KaylaR2040/SD_OrionBMS/src/bq79616.c

/* ===========================================================================
 * File: bq79616.c
 * Description: Driver for TI BQ79616 battery monitor IC.
 *
 * Notes:
 *   - This driver is designed for a single stacked device; multi-device support
 *     is possible but untested.
 *   - All functions are thread-compatible but not thread-safe; caller must
 *     serialize access to the bus and device.
 * ===========================================================================
 */

#include "master.h"


/* Key register addresses (word addresses from datasheet) */

/* Table 9-10 REQ_TYPE encoding (bits 6:4) */
typedef enum
{
    BQ_REQ_SINGLE_READ          = 0u, /* 000 */
    BQ_REQ_SINGLE_WRITE         = 1u, /* 001 */
    BQ_REQ_STACK_READ           = 2u, /* 010 */
    BQ_REQ_STACK_WRITE          = 3u, /* 011 */
    BQ_REQ_BROADCAST_READ       = 4u, /* 100 */
    BQ_REQ_BROADCAST_WRITE      = 5u, /* 101 */
    BQ_REQ_BROADCAST_WRITE_REV  = 6u  /* 110 */
    /* 111 reserved */
} bq_req_type_t;

static uint8_t tx_buf[BQ_TX_MAX];
static uint8_t rx_buf[BQ_RX_MAX];

// Function Declarations
void bq_pin_tx_to_gpio(void);
void bq_pin_tx_to_uart(void);
void bq_pin_tx_set(GPIO_PinState state);
void bq_delay_us(uint32_t us);
void bq_drive_wake_pulse(uint32_t pulse_us);
void bq_enable_dwt(void);
void bq_log_hex_internal(const char *label, const uint8_t *buf, size_t len);
static int bq79616_read_all_cells_with_timeout_(uint16_t *out_mv, size_t cell_count, uint32_t timeout_ms);

/* ------------------------------ CRC16-IBM --------------------------------- */
/* Reflected polynomial 0xA001, init 0xFFFF */
static const uint16_t crc16_table[256] = {
    0x0000,0xC0C1,0xC181,0x0140,0xC301,0x03C0,0x0280,0xC241,0xC601,0x06C0,0x0780,0xC741,0x0500,0xC5C1,0xC481,0x0440,
    0xCC01,0x0CC0,0x0D80,0xCD41,0x0F00,0xCFC1,0xCE81,0x0E40,0x0A00,0xCAC1,0xCB81,0x0B40,0xC901,0x09C0,0x0880,0xC841,
    0xD801,0x18C0,0x1980,0xD941,0x1B00,0xDBC1,0xDA81,0x1A40,0x1E00,0xDEC1,0xDF81,0x1F40,0xDD01,0x1DC0,0x1C80,0xDC41,
    0x1400,0xD4C1,0xD581,0x1540,0xD701,0x17C0,0x1680,0xD641,0xD201,0x12C0,0x1380,0xD341,0x1100,0xD1C1,0xD081,0x1040,
    0xF001,0x30C0,0x3180,0xF141,0x3300,0xF3C1,0xF281,0x3240,0x3600,0xF6C1,0xF781,0x3740,0xF501,0x35C0,0x3480,0xF441,
    0x3C00,0xFCC1,0xFD81,0x3D40,0xFF01,0x3FC0,0x3E80,0xFE41,0xFA01,0x3AC0,0x3B80,0xFB41,0x3900,0xF9C1,0xF881,0x3840,
    0x2800,0xE8C1,0xE981,0x2940,0xEB01,0x2BC0,0x2A80,0xEA41,0xEE01,0x2EC0,0x2F80,0xEF41,0x2D00,0xEDC1,0xEC81,0x2C40,
    0xE401,0x24C0,0x2580,0xE541,0x2700,0xE7C1,0xE681,0x2640,0x2200,0xE2C1,0xE381,0x2340,0xE101,0x21C0,0x2080,0xE041,
    0xA001,0x60C0,0x6180,0xA141,0x6300,0xA3C1,0xA281,0x6240,0x6600,0xA6C1,0xA781,0x6740,0xA501,0x65C0,0x6480,0xA441,
    0x6C00,0xACC1,0xAD81,0x6D40,0xAF01,0x6FC0,0x6E80,0xAE41,0xAA01,0x6AC0,0x6B80,0xAB41,0x6900,0xA9C1,0xA881,0x6840,
    0x7800,0xB8C1,0xB981,0x7940,0xBB01,0x7BC0,0x7A80,0xBA41,0xBE01,0x7EC0,0x7F80,0xBF41,0x7D00,0xBDC1,0xBC81,0x7C40,
    0xB401,0x74C0,0x7580,0xB541,0x7700,0xB7C1,0xB681,0x7640,0x7200,0xB2C1,0xB381,0x7340,0xB101,0x71C0,0x7080,0xB041,
    0x5000,0x90C1,0x9181,0x5140,0x9301,0x53C0,0x5280,0x9241,0x9601,0x56C0,0x5780,0x9741,0x5500,0x95C1,0x9481,0x5440,
    0x9C01,0x5CC0,0x5D80,0x9D41,0x5F00,0x9FC1,0x9E81,0x5E40,0x5A00,0x9AC1,0x9B81,0x5B40,0x9901,0x59C0,0x5880,0x9841,
    0x8801,0x48C0,0x4980,0x8941,0x4B00,0x8BC1,0x8A81,0x4A40,0x4E00,0x8EC1,0x8F81,0x4F40,0x8D01,0x4DC0,0x4C80,0x8C41,
    0x4400,0x84C1,0x8581,0x4540,0x8701,0x47C0,0x4680,0x8641,0x8201,0x42C0,0x4380,0x8341,0x4100,0x81C1,0x8081,0x4040
};

uint16_t bq79616_crc16(const uint8_t *data, uint16_t len)
{
    uint16_t crc = BQ_CRC16_INIT_VALUE;
    for (uint16_t i = 0; i < len; i++) {
        uint8_t idx = (uint8_t)(crc ^ data[i]);
        crc = (uint16_t)((crc >> 8) ^ crc16_table[idx]);
    }
    return crc;
}

/* Validate per datasheet: CRC computed across entire frame including CRC must be 0 */
int bq_crc_validate_full_frame(const uint8_t *frame, uint16_t frame_len)
{
    if (!frame || frame_len < BQ_FRAME_CRC_MIN_BYTES) {
        return -1;
    }
    if (bq79616_crc16(frame, frame_len) == 0u) {
        return 0;
    }
    return -2;
}








/* ----------------------------- INIT byte helpers -------------------------- */
/*
 * Command INIT (Table 9-10):
 *   bit7 = 1
 *   bits6:4 = REQ_TYPE
 *   bit3 = RSVD (0)
 *   bits2:0 = DATA_SIZE (000->1 byte ... 111->8 bytes)
 *
 * data_bytes:
 *   - writes: number of write bytes (1..8)
 *   - reads:  must be 1 because DATA[0] carries (bytes_to_return - 1)
 */
uint8_t bq_init_cmd(bq_req_type_t req, uint8_t data_bytes)
{
    if (data_bytes < BQ_CMD_DATA_BYTES_MIN) data_bytes = BQ_CMD_DATA_BYTES_MIN;
    if (data_bytes > BQ_CMD_DATA_BYTES_MAX) data_bytes = BQ_CMD_DATA_BYTES_MAX;

    uint8_t data_size_bits = (uint8_t)((data_bytes - 1u) & BQ_CMD_REQ_TYPE_MASK);
    return (uint8_t)((BQ_CMD_FRAME_TYPE << 7) | (((uint8_t)req & BQ_CMD_REQ_TYPE_MASK) << 4) | data_size_bits);
}

/*
 * Response INIT (Table 9-10 response side):
 *   bit7 = 0
 *   bits6:0 = RESPONSE_BYTE (0x00->1 byte ... 0x7F->128 bytes)
 */
uint8_t bq_rsp_len_from_init(uint8_t init_byte, uint8_t *out_len)
{
    if (!out_len) return 1u;
    if ((init_byte & BQ_INIT_RESPONSE_FLAG_MASK) != 0u) return 2u; /* not a response frame */
    uint8_t n = (uint8_t)(init_byte & BQ_INIT_RESPONSE_LEN_MASK);
    *out_len = (uint8_t)(n + 1u);
    return 0u;
}

/* ---------------------------- UART helpers (HAL) -------------------------- */

int bq_uart_tx(const uint8_t *buf, uint16_t len, uint32_t timeout_ms)
{
    if (!buf || len == 0u) return -1;
    if (HAL_UART_Transmit(&uart_bq79616, (uint8_t *)buf, len, timeout_ms) == HAL_OK) {
        return 0;
    }
    return -2;
}

int bq_uart_rx(uint8_t *buf, uint16_t len, uint32_t timeout_ms)
{
    if (!buf || len == 0u) return -1;
    if (HAL_UART_Receive(&uart_bq79616, buf, len, timeout_ms) == HAL_OK) {
        return 0;
    }
    return -2;
}

int bq_uart_txrx(const uint8_t *tx, uint16_t tx_len, uint8_t *rx, uint16_t rx_len, uint32_t timeout_ms)
{
    if (!tx || !rx || tx_len == 0u || rx_len == 0u) {
        return -1;
    }

    /* Sequential TX then RX (half-duplex safe) */
    if (HAL_UART_Transmit(&uart_bq79616, (uint8_t *)tx, tx_len, timeout_ms) != HAL_OK) {
        return -2;
    }
    if (HAL_UART_Receive(&uart_bq79616, rx, rx_len, timeout_ms) != HAL_OK) {
        return -3;
    }
    return 0;
}

/* Public single-device wrappers */
int bq79616_write(uint8_t dev_id, uint16_t reg_addr, const uint8_t *data, uint8_t len)
{
    return bq7961x_single_write(dev_id, reg_addr, data, len, BQ_FAST_TIMEOUT_MS);
}


/* Optional: explicitly set baudrate on the configured handle */
int bq7961x_uart_set_baud(uint32_t baudrate)
{
    uart_bq79616.Init.BaudRate = baudrate;
    if (HAL_UART_DeInit(&uart_bq79616) != HAL_OK) return -1;
    if (HAL_UART_Init(&uart_bq79616) != HAL_OK) return -2;
    return 0;
}

void bq_pin_tx_to_gpio(void)
{
    HAL_GPIO_DeInit(GPIOC, GPIO_PIN_4);
    GPIO_InitTypeDef g = {0};
    g.Pin = GPIO_PIN_4;
    g.Mode = GPIO_MODE_OUTPUT_PP;
    g.Pull = GPIO_PULLUP;
    g.Speed = GPIO_SPEED_FREQ_HIGH;
    HAL_GPIO_Init(GPIOC, &g);
}

void bq_pin_tx_set(GPIO_PinState state)
{
    HAL_GPIO_WritePin(BQ_GPIO_PORT, BQ_GPIO_PIN, state);
}

void bq_pin_tx_to_uart(void)
{
    HAL_GPIO_DeInit(GPIOC, GPIO_PIN_4);
    GPIO_InitTypeDef g = {0};
    g.Pin = GPIO_PIN_4;
    g.Mode = GPIO_MODE_AF_PP;
    g.Pull = GPIO_PULLUP;
    g.Speed = GPIO_SPEED_FREQ_VERY_HIGH;
    g.Alternate = GPIO_AF7_USART1;
    HAL_GPIO_Init(GPIOC, &g);
}

int bq_uart_reinit(void)
{
    bq_pin_tx_to_uart();
    if (HAL_UART_Init(&uart_bq79616) == HAL_OK) {
        return 0;
    }
    return -1;
}




void bq_drive_wake_pulse(uint32_t pulse_us)
{
    /* Host manually drives TX low to generate UART wake ping per TI spec */
    bq_pin_tx_set(GPIO_LOW);
    bq_delay_us(pulse_us);
    bq_pin_tx_set(GPIO_HIGH);
}


void bq_enable_dwt(void)
{
    /* Enable DWT cycle counter for sub-ms delays if not already on */
    if (!(CoreDebug->DEMCR & CoreDebug_DEMCR_TRCENA_Msk)) {
        CoreDebug->DEMCR |= CoreDebug_DEMCR_TRCENA_Msk;
    }
    if (!(DWT->CTRL & DWT_CTRL_CYCCNTENA_Msk)) {
        DWT->CYCCNT = 0;
        DWT->CTRL |= DWT_CTRL_CYCCNTENA_Msk;
    }
}

void bq_delay_us(uint32_t us)
{
    bq_enable_dwt();
    uint32_t cycles = (SystemCoreClock / 1000000u) * us;
    uint32_t start = DWT->CYCCNT;
    while ((DWT->CYCCNT - start) < cycles) {
        __NOP();
    }
}

/* TI-style delay wrappers */
void delayus(uint16_t us)
{
    bq_delay_us(us);
}

void delayms(uint16_t ms)
{
    HAL_Delay(ms);
}

void bq_log_hex(const char *label, const uint8_t *buf, size_t len)
{
    const char *tag = (label) ? label : "BUF";
    if (!buf || len == 0u) {
        LOG_PRINT(LOG_TYPE_INFO, "%s: <empty>", tag);
        return;
    }

    char line[BQ_HEX_LOG_LINE_MAX_CHARS];
    size_t pos = 0u;
    pos += (size_t)snprintf(line + pos, sizeof(line) - pos, "%s (%uB): ", tag, (unsigned)len);

    for (size_t i = 0; i < len; i++) {
        if ((pos + BQ_HEX_LOG_ELLIPSIS_RESERVE) >= sizeof(line)) {
            pos += (size_t)snprintf(line + pos, sizeof(line) - pos, "...");
            break;
        }
        pos += (size_t)snprintf(line + pos, sizeof(line) - pos, "%02X ", buf[i]);
    }

    LOG_PRINT(LOG_TYPE_INFO, "%s", line);
}

/* ---------------------- Frame builder (command frames) -------------------- */

int bq79616_build_single_read_frame(uint16_t reg_addr, uint8_t n_minus_1, uint8_t *out, size_t out_max, size_t *out_len)
{
    if (!out || !out_len) {
        return -1;
    }
    if (out_max < BQ_SINGLE_READ_FRAME_LEN) {
        return -2;
    }

    out[0] = BQ_SINGLE_READ_INIT_VALUE; /* INIT: Single Device Read, DATA_SIZE=1 byte */
    out[1] = (uint8_t)(DEVICE_ADDR & BQ_DEV_ADDR_MAX);
    out[2] = (uint8_t)((reg_addr >> 8) & BQ_BYTE_MASK);
    out[3] = (uint8_t)(reg_addr & BQ_BYTE_MASK);
    out[4] = n_minus_1; /* number of bytes to read minus one */

    /* CRC-16-IBM across bytes [0..4], appended as [CRC_H][CRC_L] */
    uint16_t crc = bq79616_crc16(out, 5u);
    out[5] = (uint8_t)((crc >> 8) & BQ_BYTE_MASK);
    out[6] = (uint8_t)(crc & BQ_BYTE_MASK);

    *out_len = BQ_SINGLE_READ_FRAME_LEN;
    return 0;
}

int bq79616_read_partid_once(uint8_t *partid_out)
{
    LOG_PRINT(LOG_TYPE_INFO, CYAN, "=== BQ79616 bring-up: PARTID read ===");

    uint8_t val = 0u;
    int bq_status = bq7961x_single_read(DEVICE_ADDR, BQ_PARTID_REG, &val, 1u, BQ_FIRST_READ_TIMEOUT_MS);
    if (bq_status != 0) {
        LOG_PRINT(LOG_TYPE_ERROR, CYAN, "PARTID: read failed (bq_status=%d)", bq_status);
        return bq_status;
    }

    if (partid_out) {
        *partid_out = val;
    }

    LOG_PRINT(LOG_TYPE_INFO, CYAN, "PARTID: expected=0x%02X received=0x%02X", BQ_PARTID_EXPECTED, val);
    return (val == BQ_PARTID_EXPECTED) ? 0 : 1;
}

int bq_build_cmd_frame(uint8_t *out, uint16_t out_max, bq_req_type_t req, uint8_t dev_addr, uint16_t reg_addr, const uint8_t *data, uint16_t data_len, uint16_t *out_len)
{
    if (!out || !out_len) return -1;
    *out_len = 0u;

    bool include_dev = (req == BQ_REQ_SINGLE_READ || req == BQ_REQ_SINGLE_WRITE);

    if (include_dev) {
        if (dev_addr > BQ_DEV_ADDR_MAX) return -2;
    }

    if (data_len < BQ_CMD_DATA_BYTES_MIN) return -3;

    /* Command DATA_SIZE is 3 bits => max 8 data bytes in a command frame */
    if (data_len > BQ_WRITE_MAX_BYTES) return -4;

    uint16_t include_dev_len = 0u;
    if (include_dev) {
        include_dev_len = 1u;
    }

    uint16_t needed = (uint16_t)(1u + include_dev_len + 2u + data_len + 2u);
    if (needed > out_max) return -5;

    uint16_t idx = 0u;

    out[idx++] = bq_init_cmd(req, (uint8_t)data_len);

    if (include_dev) {
        /* Table 9-11: bits7:6 should be 0, bits5:0 is device address */
        out[idx++] = (uint8_t)(dev_addr & BQ_DEV_ADDR_MAX);
    }

    /* Table 9-12: REG_ADR is 2 bytes (MSB then LSB) */
    out[idx++] = (uint8_t)((reg_addr >> 8) & BQ_BYTE_MASK);
    out[idx++] = (uint8_t)(reg_addr & BQ_BYTE_MASK);

    /* Table 9-13: DATA bytes */
    if (data && data_len) {
        memcpy(&out[idx], data, data_len);
    } else {
        memset(&out[idx], BQ_AUTO_ADDR_DUMMY_WRITE_VALUE, data_len);
    }
    idx = (uint16_t)(idx + data_len);

    /*
     * CRC bytes (datasheet):
     *   CRC remainder is appended so receiver CRC over entire frame (incl CRC) becomes 0.
     * We append CRC LSB then CRC MSB (matches TI ref style / common IBM CRC framing).
     */
    uint16_t crc = bq79616_crc16(out, idx);
    out[idx++] = (uint8_t)(crc & BQ_BYTE_MASK);         /* CRC_L */
    out[idx++] = (uint8_t)((crc >> 8) & BQ_BYTE_MASK);  /* CRC_H */

    *out_len = idx;
    return 0;
}

/* ---------------------- Internal send command APIs ------------------------ */
int bq7961x_single_write(uint8_t dev_addr, uint16_t reg_addr, const uint8_t *data, uint8_t len, uint32_t timeout_ms)
{
    if (len < BQ_CMD_DATA_BYTES_MIN || len > BQ_CMD_DATA_BYTES_MAX) return -1;

    uint16_t frame_len = 0u;
    int bq_status = bq_build_cmd_frame(tx_buf, sizeof(tx_buf),
                                BQ_REQ_SINGLE_WRITE,
                                dev_addr,
                                reg_addr,
                                data,
                                len,
                                &frame_len);
    if (bq_status != 0) return bq_status;

    return bq_uart_tx(tx_buf, frame_len, timeout_ms);
}

int bq7961x_single_read(uint8_t dev_addr, uint16_t reg_addr, uint8_t *out, uint8_t out_len, uint32_t timeout_ms)
{
    if (!out) return -1;
    if (out_len < 1u || out_len > BQ_READ_MAX_BYTES) return -2;

    /*
     * Per Table 9-13 (READ):
     *   DATA[0] specifies (bytes_to_return - 1)
     * So read request always has exactly 1 data byte.
     */
    uint8_t req_data = (uint8_t)(out_len - 1u);

    uint16_t cmd_len = 0u; // To be set by bq_build_cmd_frame
    int bq_status = bq_build_cmd_frame(tx_buf, sizeof(tx_buf),
                                BQ_REQ_SINGLE_READ,
                                dev_addr,
                                reg_addr,
                                &req_data,
                                1u,
                                &cmd_len);
    if (bq_status != 0) return bq_status;

    /* TX read request */
    bq_status = bq_uart_tx(tx_buf, cmd_len, timeout_ms);
    if (bq_status != 0) return bq_status;

    /*
     * RX response:
     *   First byte is INIT (bit7 must be 0). It contains (response_bytes-1) in bits6:0.
     */
    uint8_t init = 0u;
    bq_status = bq_uart_rx(&init, sizeof(init), timeout_ms);
    if (bq_status != 0) return -10;

    uint8_t rsp_data_len = 0u;
    if (bq_rsp_len_from_init(init, &rsp_data_len) != 0u) {
        return -11;
    }

    /* Ensure response length matches what you requested */
    if (rsp_data_len != out_len) {
        return -12;
    }

    /*
     * Remaining bytes after INIT:
     *   DEV(1) + REG(2) + DATA(out_len) + Cbq_status(2)
     */
    uint16_t remain = (uint16_t)(1u + 2u + rsp_data_len + 2u);
    if ((1u + remain) > sizeof(rx_buf)) return -13;

    rx_buf[0] = init;
    bq_status = bq_uart_rx(&rx_buf[1], remain, timeout_ms);
    if (bq_status != 0) return -14;

    uint16_t full_len = (uint16_t)(1u + remain);

    /* Cbq_status check across entire response (including Cbq_status) must be 0 */
    bq_status = bq_crc_validate_full_frame(rx_buf, full_len);
    if (bq_status != 0) return -15;

    /* Basic field checks */
    uint8_t rsp_dev = (uint8_t)(rx_buf[1] & BQ_DEV_ADDR_MAX);
    uint16_t rsp_reg = (uint16_t)((rx_buf[2] << 8) | rx_buf[3]);

    if (rsp_dev != (dev_addr & BQ_DEV_ADDR_MAX)) return -16;
    if (rsp_reg != reg_addr) return -17;

    /* Copy payload */
    memcpy(out, &rx_buf[4], rsp_data_len);
    return 0;
}






int bq7961x_broadcast_write(uint16_t reg_addr, const uint8_t *data, uint8_t len, uint32_t timeout_ms)
{
    if (len < BQ_CMD_DATA_BYTES_MIN || len > BQ_CMD_DATA_BYTES_MAX) return -1;

    uint16_t frame_len = 0u;
    int bq_status = bq_build_cmd_frame(tx_buf, sizeof(tx_buf),
                                BQ_REQ_BROADCAST_WRITE,
                                0u,
                                reg_addr,
                                data,
                                len,
                                &frame_len);
    if (bq_status != 0) return bq_status;

    return bq_uart_tx(tx_buf, frame_len, timeout_ms);
}

/* TI-style wake helper */
void bq79616_wake(void)
{
    /* Two 2.5 ms low pulses with UART temporarily released */
    HAL_UART_DeInit(&uart_bq79616);
    bq_pin_tx_to_gpio();

    bq_pin_tx_set(GPIO_LOW);
    delayus(BQ_WAKE_PULSE_US);
    bq_pin_tx_set(GPIO_HIGH);
    bq_pin_tx_to_uart();
    HAL_UART_Init(&uart_bq79616);

    HAL_UART_DeInit(&uart_bq79616);
    bq_pin_tx_to_gpio();

    bq_pin_tx_set(GPIO_LOW);
    delayus(BQ_WAKE_PULSE_US);
    bq_pin_tx_set(GPIO_HIGH);
    bq_pin_tx_to_uart();
    HAL_UART_Init(&uart_bq79616);
}

void bq79616_shutdown(void)
{
    LOG_PRINT(LOG_TYPE_INFO, CYAN, "=== FORCE BQ79616 SHUTDOWN ===");

    /*
     * Stop UART so the TX pin can be manually driven.
     * STM32 TX drives BQ RX.
     */
    HAL_UART_DeInit(&uart_bq79616);
    bq_pin_tx_to_gpio();

    /*
     * Ensure idle-high before the ping starts.
     * A ping is high-low-high, and UART idle is high.
     */
    bq_pin_tx_set(GPIO_HIGH);
    delayus(BQ_SHUTDOWN_IDLE_HIGH_US);

    /*
     * SHUTDOWN ping:
     * Hold BQ RX low for 7 ms to 10 ms.
     * Use 9 ms nominal.
     */
    bq_pin_tx_set(GPIO_LOW);
    delayus(BQ_SHUTDOWN_PING_LOW_US);
    bq_pin_tx_set(GPIO_HIGH);

    /*
     * Wait for the BQ to complete ACTIVE -> SHUTDOWN transition.
     * Datasheet says 20 ms. Use 25 ms margin.
     */
    delayms(BQ_SHUTDOWN_ENTRY_MS);

    /*
     * Leave transport disabled after shutdown, but keep the line high.
     * Do not leave BQ RX low, because that could look like another ping
     * or hold the interface in a bad state.
     */
    bq_pin_tx_set(GPIO_HIGH);

    LOG_PRINT(LOG_TYPE_INFO, CYAN, "=== BQ79616 SHUTDOWN COMPLETE ===");

    Volt_ForceDisable();
}

/* Read cell voltage from ADC (keeps device ACTIVE via periodic communication) */
int bq79616_read_cell_voltage(uint8_t dev_addr, uint8_t cell_channel, uint16_t *voltage_mv)
{
    int bq_status;
    uint8_t data[BQ_SINGLE_CELL_READ_BYTES] = {0};

    if (!voltage_mv) return -1;

    /* Cell voltage registers (2 bytes each):
       VC1=0x0014, VC2=0x0016, VC3=0x0018, VC4=0x001A, etc.
       Each channel offset by 2 bytes */
    uint16_t reg_addr = BQ_CELL_REG_BASE + (cell_channel * BQ_CELL_REG_STRIDE_BYTES);

    /* Read 2 bytes from the voltage register */
    bq_status = bq7961x_single_read(dev_addr, reg_addr, data, sizeof(data), BQ_FAST_TIMEOUT_MS);
    if (bq_status != 0) {
        return bq_status;
    }

    /* Convert raw ADC value to millivolts
       BQ79612 ADC resolution: 195.3 µV per LSB
       Formula: (raw_adc * 1953) / 10000 */
    uint16_t raw_adc = (data[0] << 8) | data[1];
    *voltage_mv = (raw_adc * BQ_CELL_MV_NUMERATOR) / BQ_CELL_MV_DENOMINATOR;

    return 0;
}

typedef struct
{
    uint8_t summary;
    uint8_t sys;
    uint8_t pwr1;
    uint8_t pwr2;
    uint8_t comm1;
    uint8_t comm2;
    uint8_t comm3;
    uint8_t ov1;
    uint8_t ov2;
    uint8_t uv1;
    uint8_t uv2;
} bq_fault_snapshot_t;

static int bq79616_read_fault_snapshot_(bq_fault_snapshot_t *snap, uint32_t timeout_ms)
{
    if (!snap) {
        return -1;
    }

    if (bq7961x_single_read(DEVICE_ADDR, FAULT_SUMMARY, &snap->summary, sizeof(snap->summary), timeout_ms) != 0) return -10;
    if (bq7961x_single_read(DEVICE_ADDR, FAULT_SYS, &snap->sys, sizeof(snap->sys), timeout_ms) != 0) return -11;
    if (bq7961x_single_read(DEVICE_ADDR, FAULT_PWR1, &snap->pwr1, sizeof(snap->pwr1), timeout_ms) != 0) return -12;
    if (bq7961x_single_read(DEVICE_ADDR, FAULT_PWR2, &snap->pwr2, sizeof(snap->pwr2), timeout_ms) != 0) return -13;
    if (bq7961x_single_read(DEVICE_ADDR, FAULT_COMM1, &snap->comm1, sizeof(snap->comm1), timeout_ms) != 0) return -14;
    if (bq7961x_single_read(DEVICE_ADDR, FAULT_COMM2, &snap->comm2, sizeof(snap->comm2), timeout_ms) != 0) return -15;
    if (bq7961x_single_read(DEVICE_ADDR, FAULT_COMM3, &snap->comm3, sizeof(snap->comm3), timeout_ms) != 0) return -16;
    if (bq7961x_single_read(DEVICE_ADDR, FAULT_OV1, &snap->ov1, sizeof(snap->ov1), timeout_ms) != 0) return -17;
    if (bq7961x_single_read(DEVICE_ADDR, FAULT_OV2, &snap->ov2, sizeof(snap->ov2), timeout_ms) != 0) return -18;
    if (bq7961x_single_read(DEVICE_ADDR, FAULT_UV1, &snap->uv1, sizeof(snap->uv1), timeout_ms) != 0) return -19;
    if (bq7961x_single_read(DEVICE_ADDR, FAULT_UV2, &snap->uv2, sizeof(snap->uv2), timeout_ms) != 0) return -20;

    return 0;
}

static void bq79616_log_fault_snapshot_(const bq_fault_snapshot_t *snap)
{
    if (!snap) {
        return;
    }

    if ((snap->summary | snap->sys | snap->pwr1 | snap->pwr2 |
         snap->comm1 | snap->comm2 | snap->comm3 |
         snap->ov1 | snap->ov2 | snap->uv1 | snap->uv2) == 0u) {
        //LOG_PRINT(LOG_TYPE_INFO, CYAN "BQ faults: none (SUMMARY=0x00 SYS=0x00 PWR1=0x00 PWR2=0x00 COMM1=0x00 COMM2=0x00 COMM3=0x00 OV1=0x00 OV2=0x00 UV1=0x00 UV2=0x00)");
    } else {
        LOG_PRINT(LOG_TYPE_WARN, CYAN "BQ faults: SUMMARY=0x%02X SYS=0x%02X PWR1=0x%02X PWR2=0x%02X COMM1=0x%02X COMM2=0x%02X COMM3=0x%02X OV1=0x%02X OV2=0x%02X UV1=0x%02X UV2=0x%02X",
                 snap->summary,
                 snap->sys,
                 snap->pwr1,
                 snap->pwr2,
                 snap->comm1,
                 snap->comm2,
                 snap->comm3,
                 snap->ov1,
                 snap->ov2,
                 snap->uv1,
                 snap->uv2);
    }
}

//TODO: Fix and use an interrupt not the last time
bool bq79616_service_task(void) // Uses BQ79616 Chip to externally read Voltages
{
    /* Check if voltage subsystem is already disabled */
    if (volt_status == FAILED) {
        return false;
    }

    static uint32_t last_keep_alive = 0;
    static uint32_t fault_check_tick = 0;
    static uint8_t consecutive_keepalive_failures = 0u;
    static uint8_t consecutive_fault_failures = 0u;
    static uint8_t fault_poll_phase = 0u;
    static uint8_t last_fault_sys = 0u;
    static uint8_t last_fault_comm1 = 0u;
    static uint8_t last_fault_pwr1 = 0u;
    static uint8_t last_fault_pwr2 = 0u;
    static uint32_t last_cell_snapshot_tick = 0u;
    static uint32_t last_fault_reg_log_tick = 0u;
    static uint32_t last_fault_summary_poll_tick = 0u;
    static bool had_runtime_fault_regs = false;
    static uint16_t last_cell_mv[MAX_VOLTAGE] = {0};
    static bool has_last_cell_snapshot = false;
    uint32_t now = HAL_GetTick();
    
    if ((now - last_keep_alive) >= BQ_KEEP_ALIVE_INTERVAL_MS) {  /* Every 20ms: beat comm timeout */
        last_keep_alive = now;

        uint8_t keep = BQ_CONTROL1_SEND_WAKE_MASK | BQ_CONTROL1_KEEP_ALIVE_MASK; /* 0x21 */
        int bq_status = bq7961x_single_write(DEVICE_ADDR,
                                             CONTROL1,
                                             &keep,
                                             1u,
                                             BQ_SERVICE_TIMEOUT_MS);

        /* Tolerate short transient comm glitches before disabling BQ. */
        if (bq_status != 0) {
            consecutive_keepalive_failures++;
            if (consecutive_keepalive_failures >= BQ_COMM_FAILURE_THRESHOLD) {
                LOG_PRINT(LOG_TYPE_ERROR, "BQ Keep-Alive Write FAILED repeatedly (%u). Disabling BQ task.",
                          (unsigned)consecutive_keepalive_failures);
                volt_status = FAILED;
                return false;
            }
            LOG_PRINT(LOG_TYPE_WARN, "BQ Keep-Alive write failed once (bq_status=%d). Retrying...", bq_status);
            return true;
        }
        consecutive_keepalive_failures = 0u;
    }

    /* Poll one diagnostic register per service slot so CAN does not get stuck
     * behind a sequence of long fault reads when BQ comms are missing.
     * Round-robin phase: FAULT_SYS -> FAULT_COMM1 -> FAULT_PWR1 -> FAULT_PWR2. */
    if ((now - fault_check_tick) >= BQ_FAULT_POLL_INTERVAL_MS) {
        uint8_t fault_val = 0u;
        int bq_status = 0;

        fault_check_tick = now;

        if (fault_poll_phase == 0u) {
            bq_status = bq7961x_single_read(DEVICE_ADDR,
                                            FAULT_SYS,
                                            &fault_val,
                                            sizeof(fault_val),
                                            BQ_SERVICE_TIMEOUT_MS);
            if (bq_status == 0) {
                last_fault_sys = fault_val;
            }
        } else if (fault_poll_phase == 1u) {
            bq_status = bq7961x_single_read(DEVICE_ADDR,
                                            FAULT_COMM1,
                                            &fault_val,
                                            sizeof(fault_val),
                                            BQ_SERVICE_TIMEOUT_MS);
            if (bq_status == 0) {
                last_fault_comm1 = fault_val;
            }
        } else if (fault_poll_phase == 2u) {
            bq_status = bq7961x_single_read(DEVICE_ADDR,
                                            FAULT_PWR1,
                                            &fault_val,
                                            sizeof(fault_val),
                                            BQ_SERVICE_TIMEOUT_MS);
            if (bq_status == 0) {
                last_fault_pwr1 = fault_val;
            }
        } else {
            bq_status = bq7961x_single_read(DEVICE_ADDR,
                                            FAULT_PWR2,
                                            &fault_val,
                                            sizeof(fault_val),
                                            BQ_SERVICE_TIMEOUT_MS);
            if (bq_status == 0) {
                last_fault_pwr2 = fault_val;
            }
        }

        if (bq_status != 0) {
            consecutive_fault_failures++;
            if (consecutive_fault_failures >= BQ_COMM_FAILURE_THRESHOLD) {
                LOG_PRINT(LOG_TYPE_ERROR, "BQ fault poll FAILED repeatedly (%u). Comm lost; disabling BQ task.",
                          (unsigned)consecutive_fault_failures);
                volt_status = FAILED;
                return false;
            }

            if (fault_poll_phase == 0u) {
                LOG_PRINT(LOG_TYPE_WARN, "BQ read failed once (sys=%d). Retrying...", bq_status);
            } else if (fault_poll_phase == 1u) {
                LOG_PRINT(LOG_TYPE_WARN, "BQ read failed once (comm1=%d). Retrying...", bq_status);
            } else if (fault_poll_phase == 2u) {
                LOG_PRINT(LOG_TYPE_WARN, "BQ read failed once (pwr1=%d). Retrying...", bq_status);
            } else {
                LOG_PRINT(LOG_TYPE_WARN, "BQ read failed once (pwr2=%d). Retrying...", bq_status);
            }
            return true;
        }

        consecutive_fault_failures = 0u;
        fault_poll_phase = (uint8_t)((fault_poll_phase + 1u) % BQ_FAULT_POLL_PHASE_COUNT);

        if ((last_fault_sys | last_fault_comm1 | last_fault_pwr1 | last_fault_pwr2) != 0u) {
            if ((now - last_fault_reg_log_tick) >= BQ_FAULT_REG_LOG_INTERVAL_MS) {
                LOG_PRINT(LOG_TYPE_WARN, "FAULT_SYS=0x%02X FAULT_COMM1=0x%02X FAULT_PWR1=0x%02X FAULT_PWR2=0x%02X",
                         last_fault_sys, last_fault_comm1, last_fault_pwr1, last_fault_pwr2);
                last_fault_reg_log_tick = now;
            }
            had_runtime_fault_regs = true;
        } else if (had_runtime_fault_regs) {
            LOG_PRINT(LOG_TYPE_INFO, "BQ runtime fault registers cleared");
            had_runtime_fault_regs = false;
        }
    }

    if ((now - last_fault_summary_poll_tick) >= BQ_FAULT_SNAPSHOT_LOG_MS) {
        bq_fault_snapshot_t snapshot = {0};
        int summary_status = bq79616_read_fault_snapshot_(&snapshot, BQ_SERVICE_TIMEOUT_MS);
        last_fault_summary_poll_tick = now;

        if (summary_status == 0) {
            last_fault_sys = snapshot.sys;
            last_fault_comm1 = snapshot.comm1;
            last_fault_pwr1 = snapshot.pwr1;
            last_fault_pwr2 = snapshot.pwr2;
            bq79616_log_fault_snapshot_(&snapshot);
        } else {
            LOG_PRINT(LOG_TYPE_WARN, "BQ fault snapshot read failed (bq_status=%d)", summary_status);
        }
    }

    if ((now - last_cell_snapshot_tick) >= BQ_CELL_SNAPSHOT_INTERVAL_MS) {
        uint16_t cell_mv[MAX_VOLTAGE] = {0};
        int cell_status = bq79616_read_all_cells_with_timeout_(cell_mv, MAX_VOLTAGE, BQ_SERVICE_TIMEOUT_MS);

        last_cell_snapshot_tick = now;

        if (cell_status == 0) {
            CAN_UpdateExternalADCVoltages(cell_mv, MAX_VOLTAGE);
            memcpy(last_cell_mv, cell_mv, sizeof(last_cell_mv));
            has_last_cell_snapshot = true;
        }
    }

    /* Logging only happens when interrupt flag fires (offset 1: every 2s, 5s, 8s...) */
    if (Timer_CheckLogOffset1Flag()) {
        if (!has_last_cell_snapshot) {
            LOG_PRINT(LOG_TYPE_WARN, "BQ cell cache unavailable yet");
        } else {
            LOG_PRINT(LOG_TYPE_INFO, GREEN, "BQ Cell Cache:");
            for (uint8_t i = 0u; i < MAX_VOLTAGE; i++) {
                const uint16_t mv = last_cell_mv[i];
                LOG_PRINT(LOG_TYPE_INFO, GREEN, "  " CYAN "%2u" GREEN "  " GREEN "VC%02u" GREEN "  " ORANGE "%4u" GREEN " -> " MAGENTA "%u.%03u V" GREEN,
                         (unsigned)(i + 1u),
                         (unsigned)(i + 1u),
                         (unsigned)mv,
                         (unsigned)(mv / THERM_MV_PER_VOLT),
                         (unsigned)(mv % THERM_MV_PER_VOLT));
            }
        }
    }
    
    return true; /* Communication is still good, keep running */
}

int bq79616_clear_startup_faults(void)
{
    int status;
    uint8_t val;
    uint8_t summary;

    /* Allow time for device to finish wake/auto-address transitions */
    HAL_Delay(BQ_STARTUP_FAULT_SETTLE_MS);

    LOG_PRINT(LOG_TYPE_INFO, CYAN, "Reading FAULT_SUMMARY before clear...");
    status = bq7961x_single_read(DEVICE_ADDR, FAULT_SUMMARY, &val, sizeof(val), BQ_FIRST_READ_TIMEOUT_MS);
    if (status != 0) {
        /* Retry a couple of times before giving up */
        HAL_Delay(BQ_STARTUP_FAULT_RETRY_DELAY_MS);
        status = bq7961x_single_read(DEVICE_ADDR, FAULT_SUMMARY, &val, sizeof(val), BQ_FIRST_READ_TIMEOUT_MS);
    }
    if (status != 0) {
        LOG_PRINT(LOG_TYPE_ERROR, CYAN, "Failed to read FAULT_SUMMARY");
        return status;
    }

    summary = val;
    LOG_PRINT(LOG_TYPE_WARN, CYAN, "FAULT_SUMMARY before clear = 0x%02X", summary);

    /* Optional detail reads */
    (void)bq7961x_single_read(DEVICE_ADDR, FAULT_SYS, &val, sizeof(val), BQ_FAST_TIMEOUT_MS);
    LOG_PRINT(LOG_TYPE_WARN, CYAN, "FAULT_SYS   = 0x%02X", val);

    (void)bq7961x_single_read(DEVICE_ADDR, FAULT_PWR1, &val, sizeof(val), BQ_FAST_TIMEOUT_MS);
    LOG_PRINT(LOG_TYPE_WARN, CYAN, "FAULT_PWR1  = 0x%02X", val);

    (void)bq7961x_single_read(DEVICE_ADDR, FAULT_PWR2, &val, sizeof(val), BQ_FAST_TIMEOUT_MS);
    LOG_PRINT(LOG_TYPE_WARN, CYAN, "FAULT_PWR2  = 0x%02X", val);

    (void)bq7961x_single_read(DEVICE_ADDR, FAULT_OV1, &val, sizeof(val), BQ_FAST_TIMEOUT_MS);
    LOG_PRINT(LOG_TYPE_WARN, CYAN, "FAULT_OV1   = 0x%02X", val);

    (void)bq7961x_single_read(DEVICE_ADDR, FAULT_OV2, &val, sizeof(val), BQ_FAST_TIMEOUT_MS);
    LOG_PRINT(LOG_TYPE_WARN, CYAN, "FAULT_OV2   = 0x%02X", val);

    (void)bq7961x_single_read(DEVICE_ADDR, FAULT_UV1, &val, sizeof(val), BQ_FAST_TIMEOUT_MS);
    LOG_PRINT(LOG_TYPE_WARN, CYAN, "FAULT_UV1   = 0x%02X", val);

    (void)bq7961x_single_read(DEVICE_ADDR, FAULT_UV2, &val, sizeof(val), BQ_FAST_TIMEOUT_MS);
    LOG_PRINT(LOG_TYPE_WARN, CYAN, "FAULT_UV2   = 0x%02X", val);

    (void)bq7961x_single_read(DEVICE_ADDR, FAULT_COMM1, &val, sizeof(val), BQ_FAST_TIMEOUT_MS);
    LOG_PRINT(LOG_TYPE_WARN, CYAN, "FAULT_COMM1 = 0x%02X", val);

    (void)bq7961x_single_read(DEVICE_ADDR, FAULT_COMM2, &val, sizeof(val), BQ_FAST_TIMEOUT_MS);
    LOG_PRINT(LOG_TYPE_WARN, CYAN, "FAULT_COMM2 = 0x%02X", val);

    (void)bq7961x_single_read(DEVICE_ADDR, FAULT_COMM3, &val, sizeof(val), BQ_FAST_TIMEOUT_MS);
    LOG_PRINT(LOG_TYPE_WARN, CYAN, "FAULT_COMM3 = 0x%02X", val);

    /* If CUST_CRC fault (bit 5 of FAULT_SUMMARY) is set, update CRC then clear */
    if (summary & BQ_FAULT_SUMMARY_CUST_CRC_BIT) {
        status = bq79616_update_cust_crc();
        if (status != 0) {
            LOG_PRINT(LOG_TYPE_WARN, CYAN, "CUST_CRC update failed (bq_status=%d); masking to allow run", status);
            (void)WriteReg(0u, FAULT_MSK2, BQ_FAULT_MASK2_CUST_CRC_MASK, 1u, FRMWRT_ALL_W);
        }
    }

    /* Clear system + power faults */
    uint64_t rst1_val = BQ_FAULT_RESET_ALL_VALUE;
    status = WriteReg(DEVICE_ADDR, FAULT_RST1, rst1_val, 2u, FRMWRT_SGL_W);
    if (status != 0) {
        LOG_PRINT(LOG_TYPE_ERROR, CYAN, "Failed to write FAULT_RST1");
        return status;
    }
    LOG_PRINT(LOG_TYPE_INFO, CYAN, "Wrote FAULT_RST1 = 0x%04X", (unsigned)rst1_val);

    /* Clear communication-related faults */
    uint64_t rst2_val = BQ_FAULT_RESET_ALL_VALUE;
    status = WriteReg(DEVICE_ADDR, FAULT_RST2, rst2_val, 2u, FRMWRT_SGL_W);
    if (status != 0) {
        LOG_PRINT(LOG_TYPE_ERROR, CYAN, "Failed to write FAULT_RST2");
        return status;
    }
    LOG_PRINT(LOG_TYPE_INFO, CYAN, "Wrote FAULT_RST2 = 0x%04X", (unsigned)rst2_val);

    HAL_Delay(BQ_POST_CLEAR_DELAY_MS);

    status = bq7961x_single_read(DEVICE_ADDR, FAULT_SUMMARY, &val, sizeof(val), BQ_FAST_TIMEOUT_MS);
    if (status != 0) {
        LOG_PRINT(LOG_TYPE_ERROR, CYAN, "Failed to read FAULT_SUMMARY after clear");
        return status;
    }

    LOG_PRINT(LOG_TYPE_INFO, CYAN, "FAULT_SUMMARY after clear = 0x%02X", val);

    if (val != 0u) {
        LOG_PRINT(LOG_TYPE_WARN, CYAN, "Fault is still present; underlying condition likely still exists");
        return 1;
    }

    LOG_PRINT(LOG_TYPE_INFO, CYAN, "Fault clear successful");
    return 0;
}

int bq79616_update_cust_crc(void)
{
    uint8_t crc_rslt[2] = {0};
    HAL_Delay(BQ_CUST_CRC_LOAD_DELAY_MS); /* allow customer area load */

    int status = bq7961x_single_read(DEVICE_ADDR, CUST_CRC_RSLT_HI, crc_rslt, 2u, BQ_FIRST_READ_TIMEOUT_MS);
    if (status != 0) {
        LOG_PRINT(LOG_TYPE_ERROR, CYAN, "CUST_CRC_RSLT read failed (bq_status=%d)", status);
        return status;
    }

    uint64_t crc_val = ((uint16_t)crc_rslt[0] << 8) | crc_rslt[1];
    status = WriteReg(DEVICE_ADDR, CUST_CRC_HI, crc_val, 2u, FRMWRT_SGL_W);
    if (status != 0) {
        LOG_PRINT(LOG_TYPE_ERROR, CYAN, "CUST_CRC write failed (bq_status=%d)", status);
        return status;
    }
    LOG_PRINT(LOG_TYPE_INFO, CYAN, "CUST_CRC updated to 0x%04X (RSLT_HI/LO=%02X%02X)", (unsigned)crc_val, crc_rslt[0], crc_rslt[1]);

    /* Clear faults after CRC update */
    (void)WriteReg(DEVICE_ADDR, FAULT_RST1, BQ_FAULT_RESET_ALL_VALUE, 2u, FRMWRT_SGL_W);
    (void)WriteReg(DEVICE_ADDR, FAULT_RST2, BQ_FAULT_RESET_ALL_VALUE, 2u, FRMWRT_SGL_W);
    HAL_Delay(BQ_POST_CLEAR_DELAY_MS);

    return 0;
}

/* Read and log key fault registers */
int bq79616_log_fault_registers(void)
{
    uint8_t val = 0;
    uint8_t summary = 0;
    int status = 0;

    status = bq7961x_single_read(DEVICE_ADDR, FAULT_SUMMARY, &summary, sizeof(summary), BQ_FIRST_READ_TIMEOUT_MS);
    if (status != 0) {
        LOG_PRINT(LOG_TYPE_ERROR, "FAULT_SUMMARY read failed (bq_status=%d)", status);
        return status;
    }
    LOG_PRINT(LOG_TYPE_INFO, "FAULT_SUMMARY=0x%02X", summary);

    if (summary != 0u) {
        if (bq7961x_single_read(DEVICE_ADDR, FAULT_SYS, &val, sizeof(val), BQ_FAST_TIMEOUT_MS) == 0)
            LOG_PRINT(LOG_TYPE_INFO, "FAULT_SYS  =0x%02X", val);
        if (bq7961x_single_read(DEVICE_ADDR, FAULT_PWR1, &val, sizeof(val), BQ_FAST_TIMEOUT_MS) == 0)
            LOG_PRINT(LOG_TYPE_INFO, "FAULT_PWR1 =0x%02X", val);
        if (bq7961x_single_read(DEVICE_ADDR, FAULT_PWR2, &val, sizeof(val), BQ_FAST_TIMEOUT_MS) == 0)
            LOG_PRINT(LOG_TYPE_INFO, "FAULT_PWR2 =0x%02X", val);
        if (bq7961x_single_read(DEVICE_ADDR, FAULT_OV1, &val, sizeof(val), BQ_FAST_TIMEOUT_MS) == 0)
            LOG_PRINT(LOG_TYPE_INFO, "FAULT_OV1  =0x%02X", val);
        if (bq7961x_single_read(DEVICE_ADDR, FAULT_OV2, &val, sizeof(val), BQ_FAST_TIMEOUT_MS) == 0)
            LOG_PRINT(LOG_TYPE_INFO, "FAULT_OV2  =0x%02X", val);
        if (bq7961x_single_read(DEVICE_ADDR, FAULT_UV1, &val, sizeof(val), BQ_FAST_TIMEOUT_MS) == 0)
            LOG_PRINT(LOG_TYPE_INFO, "FAULT_UV1  =0x%02X", val);
        if (bq7961x_single_read(DEVICE_ADDR, FAULT_UV2, &val, sizeof(val), BQ_FAST_TIMEOUT_MS) == 0)
            LOG_PRINT(LOG_TYPE_INFO, "FAULT_UV2  =0x%02X", val);
        if (bq7961x_single_read(DEVICE_ADDR, FAULT_COMM1, &val, sizeof(val), BQ_FAST_TIMEOUT_MS) == 0)
            LOG_PRINT(LOG_TYPE_INFO, "FAULT_COMM1=0x%02X", val);
        if (bq7961x_single_read(DEVICE_ADDR, FAULT_COMM2, &val, sizeof(val), BQ_FAST_TIMEOUT_MS) == 0)
            LOG_PRINT(LOG_TYPE_INFO, "FAULT_COMM2=0x%02X", val);
        if (bq7961x_single_read(DEVICE_ADDR, FAULT_COMM3, &val, sizeof(val), BQ_FAST_TIMEOUT_MS) == 0)
            LOG_PRINT(LOG_TYPE_INFO, "FAULT_COMM3=0x%02X", val);

        /* If CRC fault present, attempt update here too */
        if (summary & BQ_FAULT_SUMMARY_CUST_CRC_BIT) {
            status = bq79616_update_cust_crc();
            if (status != 0) {
                LOG_PRINT(LOG_TYPE_WARN, "CUST_CRC update (periodic) failed bq_status=%d; masking", status);
                (void)WriteReg(0u, FAULT_MSK2, BQ_FAULT_MASK2_CUST_CRC_MASK, 1u, FRMWRT_ALL_W);
            }
        }
    }

    return 0;
}

/* ----------------------------------------------------------------------------- */
/* --------- TI reference style helpers (single-device focused) ---------------- */
/* ----------------------------------------------------------------------------- */

int WriteReg(uint8_t bID, uint16_t wAddr, uint64_t dwData, uint8_t bLen, uint8_t bWriteType)
{
    if (bLen < BQ_CMD_DATA_BYTES_MIN || bLen > BQ_CMD_DATA_BYTES_MAX) {
        return -1;
    }

    uint8_t buf[BQ_CMD_DATA_BYTES_MAX] = {0};
    for (uint8_t i = 0u; i < bLen; i++) {
        /* MSB first (matches TI reference code ordering) */
        buf[i] = (uint8_t)((dwData >> (8u * (bLen - 1u - i))) & BQ_BYTE_MASK);
    }

    switch (bWriteType) {
    case FRMWRT_SGL_W:
        return bq7961x_single_write(bID, wAddr, buf, bLen, BQ_FAST_TIMEOUT_MS);
    case FRMWRT_ALL_W:
        return bq7961x_broadcast_write(wAddr, buf, bLen, BQ_FAST_TIMEOUT_MS);
    // case FRMWRT_STK_W:
    //     return bq7961x_stack_write(wAddr, buf, bLen, BQ_FAST_TIMEOUT_MS);
    // case FRMWRT_REV_ALL_W:
    //     return bq7961x_broadcast_write_reverse(wAddr, buf, bLen, BQ_FAST_TIMEOUT_MS);
    default:
        return -2;
    }
}

int ReadReg(uint8_t bID, uint16_t wAddr, uint8_t *pData, uint8_t bLen, uint32_t timeout_ms, uint8_t bWriteType)
{
    if (!pData || bLen < 1u || bLen > BQ_READ_MAX_BYTES) {
        return -1;
    }

    uint8_t dev = bID;
    /* For single-device systems treat all read types as single read */
    (void)bWriteType;

    uint8_t payload[BQ_READ_MAX_BYTES] = {0};
    int status = bq7961x_single_read(dev, wAddr, payload, bLen, timeout_ms);
    if (status != 0) {
        return status;
    }

    /* Build a response frame that mirrors TI's expected layout:
     * INIT | DEV | REG_H | REG_L | DATA... | CRC_L | CRC_H
     */
    uint8_t init = (uint8_t)((bLen - 1u) & BQ_INIT_RESPONSE_LEN_MASK); /* response_bytes-1 */
    pData[0] = init;
    pData[1] = (uint8_t)(dev & BQ_DEV_ADDR_MAX);
    pData[2] = (uint8_t)((wAddr >> 8) & BQ_BYTE_MASK);
    pData[3] = (uint8_t)(wAddr & BQ_BYTE_MASK);
    memcpy(&pData[4], payload, bLen);

    uint16_t crc = bq79616_crc16(pData, (uint16_t)(BQ_RESPONSE_PREFIX_BYTES + bLen));
    pData[4 + bLen] = (uint8_t)(crc & BQ_BYTE_MASK);
    pData[5 + bLen] = (uint8_t)((crc >> 8) & BQ_BYTE_MASK);

    return (int)(bLen + BQ_RESPONSE_FRAME_OVERHEAD_BYTES); /* total frame length returned */
}

void ResetAllFaults(uint8_t bID, uint8_t bWriteType)
{
    uint64_t rst_val = BQ_FAULT_RESET_ALL_VALUE; /* two bytes */
    (void)bID;
    if (bWriteType == FRMWRT_ALL_W) {
        (void)WriteReg(0u, FAULT_RST1, rst_val, 2u, FRMWRT_ALL_W);
    } else {
        (void)WriteReg(DEVICE_ADDR, FAULT_RST1, rst_val, 2u, FRMWRT_SGL_W);
    }
}

int bq79616_auto_address_single(void)
{
    /* TI-style single-board auto-address using broadcast */
    int status;

    /* Dummy writes to sync DLLs */
    status = WriteReg(0u, OTP_ECC_DATAIN1, BQ_AUTO_ADDR_DUMMY_WRITE_VALUE, 1u, FRMWRT_ALL_W); if (status != 0) return status;
    status = WriteReg(0u, OTP_ECC_DATAIN2, BQ_AUTO_ADDR_DUMMY_WRITE_VALUE, 1u, FRMWRT_ALL_W); if (status != 0) return status;
    status = WriteReg(0u, OTP_ECC_DATAIN3, BQ_AUTO_ADDR_DUMMY_WRITE_VALUE, 1u, FRMWRT_ALL_W); if (status != 0) return status;
    status = WriteReg(0u, OTP_ECC_DATAIN4, BQ_AUTO_ADDR_DUMMY_WRITE_VALUE, 1u, FRMWRT_ALL_W); if (status != 0) return status;
    status = WriteReg(0u, OTP_ECC_DATAIN5, BQ_AUTO_ADDR_DUMMY_WRITE_VALUE, 1u, FRMWRT_ALL_W); if (status != 0) return status;
    status = WriteReg(0u, OTP_ECC_DATAIN6, BQ_AUTO_ADDR_DUMMY_WRITE_VALUE, 1u, FRMWRT_ALL_W); if (status != 0) return status;
    status = WriteReg(0u, OTP_ECC_DATAIN7, BQ_AUTO_ADDR_DUMMY_WRITE_VALUE, 1u, FRMWRT_ALL_W); if (status != 0) return status;
    status = WriteReg(0u, OTP_ECC_DATAIN8, BQ_AUTO_ADDR_DUMMY_WRITE_VALUE, 1u, FRMWRT_ALL_W); if (status != 0) return status;

    /* Enable AUTO_ADDR */
    status = WriteReg(0u, CONTROL1, BQ_AUTO_ADDR_ENABLE_VALUE, 1u, FRMWRT_ALL_W); if (status != 0) return status;

    /* Set address of the single board to 0 */
    status = WriteReg(0u, DIR0_ADDR, BQ_AUTO_ADDR_DEVICE_ADDR_VALUE, 1u, FRMWRT_ALL_W); if (status != 0) return status;

    /* Set all to stack mode then single device base+top */
    status = WriteReg(0u, COMM_CTRL, BQ_COMM_CTRL_STACK_MODE_VALUE, 1u, FRMWRT_ALL_W); if (status != 0) return status;
    status = WriteReg(0u, COMM_CTRL, BQ_COMM_CTRL_BASE_TOP_VALUE, 1u, FRMWRT_SGL_W); if (status != 0) return status;

    /* Throw-away reads to sync DLL */
    uint8_t dummy[2];
    (void)ReadReg(0u, OTP_ECC_DATAIN1, dummy, 1u, BQ_FAST_TIMEOUT_MS, FRMWRT_ALL_R);
    (void)ReadReg(0u, OTP_ECC_DATAIN2, dummy, 1u, BQ_FAST_TIMEOUT_MS, FRMWRT_ALL_R);
    (void)ReadReg(0u, OTP_ECC_DATAIN3, dummy, 1u, BQ_FAST_TIMEOUT_MS, FRMWRT_ALL_R);
    (void)ReadReg(0u, OTP_ECC_DATAIN4, dummy, 1u, BQ_FAST_TIMEOUT_MS, FRMWRT_ALL_R);
    (void)ReadReg(0u, OTP_ECC_DATAIN5, dummy, 1u, BQ_FAST_TIMEOUT_MS, FRMWRT_ALL_R);
    (void)ReadReg(0u, OTP_ECC_DATAIN6, dummy, 1u, BQ_FAST_TIMEOUT_MS, FRMWRT_ALL_R);
    (void)ReadReg(0u, OTP_ECC_DATAIN7, dummy, 1u, BQ_FAST_TIMEOUT_MS, FRMWRT_ALL_R);
    (void)ReadReg(0u, OTP_ECC_DATAIN8, dummy, 1u, BQ_FAST_TIMEOUT_MS, FRMWRT_ALL_R);

    /* Clear comm faults */
    (void)WriteReg(0u, FAULT_RST2, BQ_FAULT_RST2_COMM_CLEAR_VALUE, 1u, FRMWRT_ALL_W);

    return 0;
}

int bq79616_config_main_adc(void)
{
    /* Configure exact active-cell count, LPF 26 Hz, continuous + MAIN_GO. */
    int status;
    uint8_t num_cells_configured = (MAX_VOLTAGE < BQ_ACTIVE_CELL_MIN) ? BQ_ACTIVE_CELL_MIN : (uint8_t)MAX_VOLTAGE;
    if (num_cells_configured > BQ_ACTIVE_CELL_MAX) {
        num_cells_configured = BQ_ACTIVE_CELL_MAX;
    }
    uint8_t active_cell_num_value = (uint8_t)(num_cells_configured - BQ_ACTIVE_CELL_ENCODING_OFFSET);

    status = WriteReg(DEVICE_ADDR, ACTIVE_CELL, active_cell_num_value, 1u, FRMWRT_SGL_W);
    if (status != 0) return status;

    status = WriteReg(DEVICE_ADDR, ADC_CONF1, BQ_ADC_CONF1_VALUE, 1u, FRMWRT_SGL_W);
    if (status != 0) return status;

    status = WriteReg(DEVICE_ADDR, ADC_CTRL1, BQ_ADC_CTRL1_CONTINUOUS_MAIN_GO, 1u, FRMWRT_SGL_W); /* continuous + LPF + MAIN_GO */
    if (status != 0) return status;

    /* Allow LPF to settle: 38 ms + small margin */
    bq_delay_us(BQ_LPF_SETTLE_BASE_US + (BQ_LPF_SETTLE_PER_STACK_US * BQ_STACK_COUNT));
    return 0;
}

int bq79616_init_device(void)
{
    int status;

    /* Two wake tones (TI sample calls Wake twice) */
    bq79616_wake();

    /* Allow settle after shutdown->active transition */
    bq_delay_us(BQ_STARTUP_SETTLE_US);

    /* Clear any startup faults (best-effort) */
    ResetAllFaults(DEVICE_ADDR, FRMWRT_SGL_W);

    /* Configure ADC for continuous conversion */
    status = bq79616_config_main_adc();
    return status;
}



bool bq79616_try_init(void)
{
    int bq_status;
    int clear_status;
    uint8_t partid = 0u;

    /* Keep this path tolerant: BQ is optional for thermistor CAN operation. */
    bq79616_auto_address_single();

    bq_status = bq79616_init_device();
    if (bq_status != 0) {
        LOG_PRINT(LOG_TYPE_WARN, CYAN, "BQ init failed (bq_status=%d). Continuing with ADC/CAN only.", bq_status);
        return false;
    }

    if (bq79616_read_partid_once(&partid) == 0) {
        LOG_PRINT(LOG_TYPE_INFO, CYAN, "BQ79616 PARTID->0x%02X", partid);
    } else {
        LOG_PRINT(LOG_TYPE_WARN, CYAN, "BQ PARTID read failed after init. Continuing with BQ keep-alive attempt.");
    }

    /* Best-effort startup fault clear (including CUST_CRC handling). */
    clear_status = bq79616_clear_startup_faults();
    if (clear_status != 0) {
        LOG_PRINT(LOG_TYPE_WARN, CYAN, "BQ startup fault clear returned %d; continuing with BQ active.", clear_status);
    }

    return true;
}

static int bq79616_read_all_cells_with_timeout_(uint16_t *out_mv, size_t cell_count, uint32_t timeout_ms)
{
    if (!out_mv || cell_count == 0u || cell_count > BQ_READ_ALL_CELLS_COUNT) {
        return -1;
    }

    uint8_t raw[BQ_READ_ALL_CELLS_RAW_BYTES] = {0};
    uint16_t parsed_mv[BQ_READ_ALL_CELLS_COUNT] = {0};
    int status = bq7961x_single_read(DEVICE_ADDR, VCELL16_HI, raw, BQ_READ_ALL_CELLS_RAW_BYTES, timeout_ms);
    if (status != 0) {
        return status;
    }

    /* VCELL16_HI .. VCELL1_LO, 2 bytes per cell, descending cell order */
    for (size_t i = 0; i < BQ_READ_ALL_CELLS_COUNT; i++) {
        size_t byte_idx = i * 2u;
        uint16_t adc_raw = (uint16_t)((raw[byte_idx] << 8) | raw[byte_idx + 1u]);

        /* Convert to mV using 190.73 uV/LSB */
        uint32_t mv = (uint32_t)adc_raw * BQ_ALL_CELLS_MV_NUMERATOR;
        mv = mv / BQ_ALL_CELLS_MV_DENOMINATOR;

        /* Map so parsed_mv[0] corresponds to cell 1 (ascending order) */
        size_t cell = BQ_READ_ALL_CELLS_COUNT - i;           /* cell number (16..1) */
        size_t idx_out = cell - 1u;      /* zero-based */
        parsed_mv[idx_out] = (uint16_t)mv;

        /* Add calibration offset for cells 1 and 14 */
        if (idx_out == BQ_CELL1_INDEX) {
            parsed_mv[idx_out] = (uint16_t)(mv + BQ_CELL1_CAL_OFFSET_MV);
        } else if (idx_out == BQ_CELL14_INDEX){
            parsed_mv[idx_out] = (uint16_t)(mv + BQ_CELL14_CAL_OFFSET_MV);
        } else{
            parsed_mv[idx_out] = (uint16_t)mv;
        }
    }

    for (size_t i = 0; i < cell_count; i++) {
        out_mv[i] = parsed_mv[i];
    }

    return 0;
}

int bq79616_read_all_cells(uint16_t *out_mv, size_t cell_count)
{
    return bq79616_read_all_cells_with_timeout_(out_mv, cell_count, BQ_FAST_TIMEOUT_MS);
}
