KaylaR2040/SD_OrionBMS/src/can_messages.c

/*
 * File: can_messages.c
 * Description: CAN message encoding for thermistor modules and Orion BMS
 */

#include "master.h"
#include "therm.h" /* for THERM_REF_MV and THERM_MAX_COUNTS */

ThermistorCache_t s_cache = {0};
static uint16_t s_prev_fault_mask = 0u;
static uint16_t s_prev_hot_mask = 0u;
static bool s_prev_pack_hot = false;
static uint32_t s_last_fault_summary_log_ms = 0u;

/* Module configuration (source address 0x80 = first Orion thermistor module) */
static const ThermJ1939ClaimMsg_t s_default_claim = {
    .unique_id = { ORION_CLAIM_UNIQUE_ID0, ORION_CLAIM_UNIQUE_ID1, ORION_CLAIM_UNIQUE_ID2 },
    .bms_target = ORION_BMS_TARGET_ADDR,
    .thermistor_module = ORION_THERM_MODULE_INDEX,
    .constant = { ORION_CLAIM_CONSTANT0, ORION_CLAIM_CONSTANT1, ORION_CLAIM_CONSTANT2 }
};

static uint16_t CAN_ThermMask(uint8_t therm_index)
{
    return (uint16_t)(1u << therm_index);
}

static const char *CAN_ThermFaultReason_(const ThermistorCache_t *cache, uint8_t idx)
{
    if ((cache == NULL) || (idx >= cache->count)) {
        return "unknown";
    }

    if (CAN_Debug_IsSensorFaulted(idx)) {
        return "forced";
    }
    if (cache->adc_raw[idx] >= ORION_THERM_ADC_OPEN_FAULT_THRESHOLD) {
        return "open";
    }
    if (cache->adc_raw[idx] <= ORION_THERM_ADC_SHORT_FAULT_THRESHOLD) {
        return "short";
    }
    if ((cache->temps[idx] < ORION_THERM_MIN_VALID_C) ||
        (cache->temps[idx] > ORION_THERM_MAX_VALID_C)) {
        return "range";
    }

    return "invalid";
}

static void CAN_LogActiveFaultChannels_(const ThermistorCache_t *cache, uint16_t fault_mask)
{
    if ((cache == NULL) || (fault_mask == 0u)) {
        return;
    }

    for (uint8_t i = 0u; i < cache->count; i++) {
        const uint16_t therm_mask = CAN_ThermMask(i);
        if ((fault_mask & therm_mask) == 0u) {
            continue;
        }

        LOG_PRINT(LOG_TYPE_WARN, "Fault active: therm=%u reason=%s adc=%u temp=%dC",
                 (unsigned)(i + 1u),
                 CAN_ThermFaultReason_(cache, i),
                 (unsigned)cache->adc_raw[i],
                 (int)cache->temps[i]);
    }
}

static uint8_t CAN_PackTemp(int8_t temp_c)
{
    return (uint8_t)temp_c;
}


static uint8_t CAN_ComputeBmsChecksum(const uint8_t *payload)
{
    uint16_t sum = CAN_BMS_CHECKSUM_BASE + CAN_FRAME_LEN_BYTES;

    for (uint8_t i = 0U; i < CAN_BMS_CHECKSUM_DATA_BYTES; i++) {
        sum += (uint8_t)payload[i];
    }

    return (uint8_t)sum;
}

static uint16_t CAN_GlobalThermistorIdForModule(uint8_t module_index, uint8_t local_index)
{
    return (uint16_t)((uint16_t)module_index * CAN_GLOBAL_THERM_STRIDE) + (uint16_t)local_index;
}

static bool CAN_DebugDualModuleActive(void)
{
    return CAN_Debug_IsEnabled() && CAN_Debug_IsDualModuleEmulationEnabled();
}

static bool CAN_ModuleFaultActive(const ThermistorCache_t *cache)
{
    if (Volt_IsFaultReportingMode()) {
        return true;
    }

    return (cache != NULL) && cache->module_fault;
}

static uint32_t CAN_ClaimIdForSource(uint8_t source_addr)
{
    return THERM_J1939_CLAIM_ID_BASE | (uint32_t)source_addr;
}

static uint32_t CAN_BmsIdForSource(uint8_t source_addr)
{
    return THERM_BMS_BROADCAST_ID_BASE |
           ((uint32_t)ORION_BMS_TARGET_ADDR << CAN_SOURCE_ADDR_SHIFT_BITS) |
           (uint32_t)source_addr;
}

static uint32_t CAN_GeneralIdForSource(uint8_t source_addr)
{
    return THERM_GENERAL_BROADCAST_ID_BASE |
           ((uint32_t)ORION_BMS_TARGET_ADDR << CAN_SOURCE_ADDR_SHIFT_BITS) |
           (uint32_t)source_addr;
}

static uint32_t CAN_ExternalADCVoltageIdForSegment(uint8_t segment_index)
{
    return EXTERNAL_ADC_VOLTAGE_BASE_ID | (uint32_t)(segment_index & CAN_EXTV_SEGMENT_INDEX_MASK);
}

static void CAN_LogTxFailure_(const char *frame_name, uint32_t can_id, int result)
{
    static uint32_t last_drop_log_ms = 0U;
    static uint32_t dropped_frames = 0U;
    const uint32_t now = HAL_GetTick();

    if (result == CAN_TX_RESULT_TRANSIENT_DROP) {
        dropped_frames++;
        if ((now - last_drop_log_ms) >= CAN_TX_DROP_LOG_PERIOD_MS) {
            LOG_PRINT(LOG_TYPE_WARN, "CAN TX congested/no-ack: dropped=%lu last=%s id=0x%08lX",
                     (unsigned long)dropped_frames,
                     frame_name,
                     (unsigned long)can_id);
            last_drop_log_ms = now;
            dropped_frames = 0U;
        }
        return;
    }

    LOG_PRINT(LOG_TYPE_WARN, "\x1b[36mTX 0x%08lX %s failed result=%d",
             (unsigned long)can_id,
             frame_name,
             result);
}

static void CAN_LogExternalVoltageTx_(uint32_t ext_id,
                                      uint8_t segment_index,
                                      const uint8_t payload[CAN_FRAME_LEN_BYTES],
                                      uint32_t now_ms)
{
    static uint32_t s_last_any_ms = 0u;
    static uint32_t s_last_segment_ms[EXTERNAL_ADC_VOLTAGE_FRAMES] = {0u};
    uint32_t dt_any_ms = 0u;
    uint32_t dt_segment_ms = 0u;

    if (!CAN_Debug_IsStreamEnabled()) {
        return;
    }

    if (s_last_any_ms != 0u) {
        dt_any_ms = now_ms - s_last_any_ms;
    }
    s_last_any_ms = now_ms;

    if (segment_index < EXTERNAL_ADC_VOLTAGE_FRAMES) {
        if (s_last_segment_ms[segment_index] != 0u) {
            dt_segment_ms = now_ms - s_last_segment_ms[segment_index];
        }
        s_last_segment_ms[segment_index] = now_ms;
    }

    LOG_PRINT(LOG_TYPE_DEBUG, MAGENTA, "TX 0x%08lX extv seg=%u dt_any=%lums dt_seg=%lums [%02X %02X %02X %02X %02X %02X %02X %02X]",
              (unsigned long)ext_id,
              segment_index,
              (unsigned long)dt_any_ms,
              (unsigned long)dt_segment_ms,
              payload[0], payload[1], payload[2], payload[3],
              payload[4], payload[5], payload[6], payload[7]);
}

static void CAN_EncodeJ1939ClaimForModule(uint8_t source_addr, uint8_t module_index, uint8_t *payload)
{
    payload[0] = ORION_CLAIM_UNIQUE_ID0;         /* 0xF3 */
    payload[1] = ORION_CLAIM_UNIQUE_ID1;         /* 0x00 */
    payload[2] = source_addr;                    /* 0x80, 0x81, ... */
    payload[3] = ORION_BMS_TARGET_ADDR;          /* 0xF3 */
    payload[4] = (uint8_t)(module_index << ORION_CLAIM_MODULE_INDEX_SHIFT);   /* module index << 3 */
    payload[5] = s_default_claim.constant[0];    /* 0x40 */
    payload[6] = s_default_claim.constant[1];    /* 0x1E */
    payload[7] = s_default_claim.constant[2];    /* 0x90 */
}

static void CAN_EncodeExternalADCVoltage(uint8_t segment_index,
                                         const uint16_t *out_mv,
                                         uint8_t count,
                                         uint8_t *payload)
{
    const uint8_t clamped_count = (count > MAX_VOLTAGE) ? MAX_VOLTAGE : count;
    const uint8_t start_index = (uint8_t)(segment_index * EXTERNAL_ADC_VOLTAGES_PER_FRAME);

    memset(payload, 0, CAN_FRAME_LEN_BYTES);

    for (uint8_t slot = 0u; slot < EXTERNAL_ADC_VOLTAGES_PER_FRAME; slot++) {
        const uint8_t value_index = (uint8_t)(start_index + slot);
        uint16_t millivolts = 0u;

        if ((out_mv != NULL) && (value_index < clamped_count)) {
            millivolts = out_mv[value_index];
        }

        payload[(uint8_t)(slot * 2u)] = (uint8_t)(millivolts & CAN_BYTE_MASK);
        payload[(uint8_t)(slot * 2u + 1u)] = (uint8_t)((millivolts >> CAN_SOURCE_ADDR_SHIFT_BITS) & CAN_BYTE_MASK);
    }
}

static void CAN_EncodeBmsForCache(const ThermistorCache_t *cache,
                                  uint8_t module_index,
                                  uint8_t *payload)
{
    const uint8_t enabled = (uint8_t)(cache->valid_count & CAN_ENABLED_COUNT_MASK);

    payload[0] = module_index;                    /* Module number (zero-based) */
    payload[1] = CAN_PackTemp(cache->min_temp);   /* Lowest temp (int8_t) */
    payload[2] = CAN_PackTemp(cache->max_temp);   /* Highest temp (int8_t) */
    payload[3] = CAN_PackTemp(cache->avg_temp);   /* Average temp (int8_t) */

    uint8_t module_fault_flag = 0u;
    if (CAN_ModuleFaultActive(cache)) {
        module_fault_flag = CAN_MODULE_FAULT_FLAG_MASK;
    }

    payload[4] = (uint8_t)(enabled | module_fault_flag);
    payload[5] = cache->max_id;                   /* Highest loaded thermistor ID on module */
    payload[6] = cache->min_id;                   /* Lowest loaded thermistor ID on module */
    payload[7] = CAN_ComputeBmsChecksum(payload);
}

static void CAN_EncodeGeneralForCache(const ThermistorCache_t *cache,
                                      uint8_t module_index,
                                      uint8_t therm_index,
                                      uint8_t *payload)
{
    uint8_t capped_idx = 0U;
    if (therm_index < cache->count) {
        capped_idx = therm_index;
    }

    int8_t this_temp = 0;
    if (cache->count > 0U && therm_index < cache->count) {
        this_temp = cache->temps[therm_index];
    }

    const uint16_t global_id = CAN_GlobalThermistorIdForModule(module_index, capped_idx);
    const bool therm_fault = (cache->fault_mask & CAN_ThermMask(capped_idx)) != 0u;

    payload[0] = (uint8_t)(global_id & CAN_BYTE_MASK);                                      /* Global ID low byte */
    payload[1] = (uint8_t)((global_id >> CAN_SOURCE_ADDR_SHIFT_BITS) & CAN_BYTE_MASK);      /* Global ID high byte */
    payload[2] = CAN_PackTemp(this_temp);                   /* Thermistor value (int8_t) */

    uint8_t therm_fault_flag = 0u;
    if (therm_fault) {
        therm_fault_flag = CAN_THERM_FAULT_FLAG_MASK;
    }

    payload[3] = (uint8_t)(capped_idx | therm_fault_flag);
    payload[4] = CAN_PackTemp(cache->min_temp);             /* Lowest valid temp on module */
    payload[5] = CAN_PackTemp(cache->max_temp);             /* Highest valid temp on module */
    payload[6] = cache->max_id;                             /* Highest loaded thermistor ID on module */
    payload[7] = cache->min_id;                             /* Lowest loaded thermistor ID on module */

    CAN_Debug_SetLastGeneralInfo(global_id, capped_idx, this_temp);
}

static bool CAN_SendExternalADCVoltageFrame_(uint8_t segment_index, uint8_t *payload)
{
    if ((payload == NULL) || (g_can_ctx.voltages.num_active == 0u)) {
        return false;
    }

    {
        const uint32_t ext_id = CAN_ExternalADCVoltageIdForSegment(segment_index);
        int result;

        CAN_EncodeExternalADCVoltage(segment_index,
                                     g_can_ctx.voltages.voltage_adc_values,
                                     g_can_ctx.voltages.num_active,
                                     payload);

        result = CAN_Comm_SendExt(ext_id, payload, CAN_FRAME_LEN_BYTES);
        if (result != 0) {
            CAN_LogTxFailure_("extv", ext_id, result);
            return false;
        }

        CAN_LogExternalVoltageTx_(ext_id, segment_index, payload, HAL_GetTick());
    }

    return true;
}

static uint8_t CAN_DebugModuleSampleCount(uint8_t start_idx)
{
    const uint8_t active = g_can_ctx.thermistors.num_active;
    if (active <= start_idx) {
        return 0U;
    }

    const uint8_t remaining = (uint8_t)(active - start_idx);
    if (remaining > CAN_DEBUG_EMU_CHANNELS_PER_MODULE) {
        return CAN_DEBUG_EMU_CHANNELS_PER_MODULE;
    }
    return remaining;
}

static void CAN_BuildModuleCacheFromAdc(uint8_t start_idx,
                                        uint8_t module_count,
                                        ThermistorCache_t *cache)
{
    if (cache == NULL) {
        return;
    }

    memset(cache, 0, sizeof(*cache));
    if (module_count > CAN_DEBUG_EMU_CHANNELS_PER_MODULE) {
        cache->count = CAN_DEBUG_EMU_CHANNELS_PER_MODULE;
    } else {
        cache->count = module_count;
    }

    cache->min_temp = ORION_THERM_MAX_VALID_C;
    cache->max_temp = ORION_THERM_MIN_VALID_C;
    cache->min_id = 0U;
    cache->max_id = (cache->count > 0U) ? (uint8_t)(cache->count - 1U) : 0U;

    int32_t sum = 0;
    for (uint8_t local_idx = 0U; local_idx < cache->count; local_idx++) {
        const uint8_t abs_idx = (uint8_t)(start_idx + local_idx);
        const uint16_t adc_raw = g_can_ctx.thermistors.thermistor_adc_values[abs_idx];
        int8_t temp_c = Thermistor_ADCToTemp(adc_raw);

        bool therm_fault = false;
        bool therm_too_hot = false;
        const bool sensor_fault_forced = CAN_Debug_IsSensorFaulted(abs_idx);

        int8_t override_temp = 0;
        const bool has_override = CAN_Debug_GetTempOverride(abs_idx, &override_temp);
        const bool debug_override_active = CAN_Debug_IsEnabled() && has_override;

        if (debug_override_active) {
            temp_c = override_temp;
            therm_fault = false;
        } else {
            if (adc_raw >= ORION_THERM_ADC_OPEN_FAULT_THRESHOLD ||
                adc_raw <= ORION_THERM_ADC_SHORT_FAULT_THRESHOLD ||
                temp_c < ORION_THERM_MIN_VALID_C ||
                temp_c > ORION_THERM_MAX_VALID_C) {
                therm_fault = true;
            }
        }

        if (!therm_fault && temp_c > ORION_THERM_HOT_THRESHOLD_C) {
            therm_too_hot = true;
        }

        if (sensor_fault_forced) {
            therm_fault = true;
        }

        cache->adc_raw[local_idx] = adc_raw;
        cache->temps[local_idx] = temp_c;

        /* Keep over-temperature channels "valid" so Orion sees the hot value in min/max/avg.
         * Reserve thermistor fault bits for truly invalid channels (open/short/forced sensor fault). */
        if (therm_fault) {
            cache->fault_mask |= CAN_ThermMask(local_idx);
            cache->module_fault = true;
            continue;
        }

        if (therm_too_hot) {
            const uint32_t millivolts = ((uint32_t)adc_raw * (uint32_t)THERM_REF_MV) / (uint32_t)THERM_MAX_COUNTS;
            LOG_PRINT(LOG_TYPE_WARN, "Thermistor %u too hot: %dC (adc=%u, %lu.%03lu V)",
                     (unsigned)(abs_idx + 1U), (int)temp_c,
                     (unsigned)adc_raw,
                     (unsigned long)(millivolts / THERM_MV_PER_VOLT),
                     (unsigned long)(millivolts % THERM_MV_PER_VOLT));
        }

        if (temp_c < cache->min_temp) {
            cache->min_temp = temp_c;
        }
        if (temp_c > cache->max_temp) {
            cache->max_temp = temp_c;
        }
        sum += temp_c;
        cache->valid_count++;
    }

    if (cache->valid_count > 0U) {
        cache->avg_temp = (int8_t)(sum / (int32_t)cache->valid_count);
    } else {
        cache->min_temp = 0;
        cache->max_temp = 0;
        cache->avg_temp = 0;
    }

    cache->last_update_ms = HAL_GetTick();
}


/* -------------------------------------------------------------------------- */
/* ADC to Temperature Conversion                                              */
/* -------------------------------------------------------------------------- */

void ConvertAllThermistors(const uint16_t *adc_values, uint8_t count)
{
    if (!adc_values) {
        return;
    }

    if (count > MAX_THERMISTORS) {
        s_cache.count = MAX_THERMISTORS;
    } else {
        s_cache.count = count;
    }
    s_cache.valid_count = 0u;
    s_cache.min_temp = ORION_THERM_MAX_VALID_C;
    s_cache.max_temp = ORION_THERM_MIN_VALID_C;
    /* Orion bytes 6/7 report the module's loaded thermistor range, not hottest/coldest IDs. */
    s_cache.min_id = 0U;
    if (s_cache.count > 0U) {
        s_cache.max_id = (uint8_t)(s_cache.count - 1U);
    } else {
        s_cache.max_id = 0U;
    }
    s_cache.fault_mask = 0u;
    s_cache.module_fault = false;

    uint16_t hot_mask = 0u;
    int32_t sum = 0;
    for (uint8_t i = 0; i < s_cache.count; i++) {
        const uint16_t adc_raw = adc_values[i];
        int8_t temp_c = Thermistor_ADCToTemp(adc_raw);
        const uint16_t therm_mask = CAN_ThermMask(i);
        bool therm_fault = false;
        const bool sensor_fault_forced = CAN_Debug_IsSensorFaulted(i);

        int8_t override_temp = 0;
        const bool has_override = CAN_Debug_GetTempOverride(i, &override_temp);
        const bool debug_override_active = CAN_Debug_IsEnabled() && has_override;

        if (debug_override_active) {
            temp_c = override_temp;
            therm_fault = false; /* ignore ADC/range faults when we explicitly override */
        } else {
            if (adc_raw >= ORION_THERM_ADC_OPEN_FAULT_THRESHOLD ||
                adc_raw <= ORION_THERM_ADC_SHORT_FAULT_THRESHOLD ||
                temp_c < ORION_THERM_MIN_VALID_C ||
                temp_c > ORION_THERM_MAX_VALID_C) {
                therm_fault = true;
            }
        }

        /* Track over-temperature separately from invalid-sensor faults.
         * Over-temp must remain valid in CAN stats so BMS can report a hot condition. */
        if (!therm_fault && temp_c > ORION_THERM_HOT_THRESHOLD_C) {
            hot_mask |= therm_mask;
            if ((s_prev_hot_mask & therm_mask) == 0u) {
                const uint32_t millivolts = ((uint32_t)adc_raw * (uint32_t)THERM_REF_MV) / (uint32_t)THERM_MAX_COUNTS;
                LOG_PRINT(LOG_TYPE_WARN, "Thermistor %u too hot: %dC (adc=%u, %lu.%03lu V)",
                         (unsigned)(i + 1U), (int)temp_c,
                         (unsigned)adc_raw,
                         (unsigned long)(millivolts / THERM_MV_PER_VOLT),
                         (unsigned long)(millivolts % THERM_MV_PER_VOLT));
            }
        }

        if (sensor_fault_forced) {
            therm_fault = true;
        }

        s_cache.adc_raw[i] = adc_raw;
        s_cache.temps[i] = temp_c;

        if (therm_fault) {
            s_cache.fault_mask |= therm_mask;
            s_cache.module_fault = true;
            if ((s_prev_fault_mask & therm_mask) == 0u) {
                LOG_PRINT(LOG_TYPE_WARN, "Thermistor %u fault set (mask=0x%04X) adc=%u temp=%dC",
                         (unsigned)(i + 1U),
                         (unsigned)s_cache.fault_mask,
                         (unsigned)adc_raw,
                         (int)temp_c);
            }
            continue;
        }

        if ((s_prev_fault_mask & therm_mask) != 0u) {
            LOG_PRINT(LOG_TYPE_INFO, "Thermistor %u fault cleared adc=%u temp=%dC",
                     (unsigned)(i + 1U),
                     (unsigned)adc_raw,
                     (int)temp_c);
        }

        if (temp_c < s_cache.min_temp) {
            s_cache.min_temp = temp_c;
        }
        if (temp_c > s_cache.max_temp) {
            s_cache.max_temp = temp_c;
        }
        sum += temp_c;
        s_cache.valid_count++;
    }

    if (s_cache.valid_count > 0U) {
        s_cache.avg_temp = (int8_t)(sum / (int32_t)s_cache.valid_count);
    } else {
        s_cache.min_temp = 0;
        s_cache.max_temp = 0;
        s_cache.avg_temp = 0;
        s_cache.min_id = 0U;
        if (s_cache.count > 0U) {
            s_cache.max_id = (uint8_t)(s_cache.count - 1U);
        } else {
            s_cache.max_id = 0U;
        }
    }

    const uint32_t now_ms = HAL_GetTick();
    s_cache.last_update_ms = now_ms;

    for (uint8_t i = 0u; i < s_cache.count; i++) {
        const uint16_t therm_mask = CAN_ThermMask(i);
        if (((s_prev_hot_mask & therm_mask) != 0u) &&
            ((hot_mask & therm_mask) == 0u)) {
            LOG_PRINT(LOG_TYPE_INFO, "Thermistor %u no longer too hot", (unsigned)(i + 1U));
        }
    }

    const bool pack_too_hot = (s_cache.max_temp > ORION_THERM_HOT_THRESHOLD_C);
    if (pack_too_hot && !s_prev_pack_hot) {
        LOG_PRINT(LOG_TYPE_WARN, "PACK TOO HOT: max=%dC id=%u", (int)s_cache.max_temp, (unsigned)s_cache.max_id);
    }
    if (!pack_too_hot && s_prev_pack_hot) {
        LOG_PRINT(LOG_TYPE_INFO, "PACK TEMP NORMALIZED: max=%dC", (int)s_cache.max_temp);
    }
    s_prev_pack_hot = pack_too_hot;

    if (s_cache.fault_mask != s_prev_fault_mask) {
        if (s_cache.fault_mask != 0u) {
            LOG_PRINT(LOG_TYPE_WARN, "Thermistor fault mask=0x%04X valid=%u",
                     (unsigned)s_cache.fault_mask,
                     (unsigned)s_cache.valid_count);
            CAN_LogActiveFaultChannels_(&s_cache, s_cache.fault_mask);
        } else {
            LOG_PRINT(LOG_TYPE_INFO, "Thermistor fault mask cleared valid=%u", (unsigned)s_cache.valid_count);
        }
        s_last_fault_summary_log_ms = now_ms;
    } else if ((s_cache.fault_mask != 0u) &&
               ((now_ms - s_last_fault_summary_log_ms) >= THERM_FAULT_PERSIST_LOG_MS)) {
        LOG_PRINT(LOG_TYPE_WARN, "Thermistor fault persists mask=0x%04X valid=%u",
                 (unsigned)s_cache.fault_mask,
                 (unsigned)s_cache.valid_count);
        CAN_LogActiveFaultChannels_(&s_cache, s_cache.fault_mask);
        s_last_fault_summary_log_ms = now_ms;
    }

    s_prev_fault_mask = s_cache.fault_mask;
    s_prev_hot_mask = hot_mask;

    CAN_Debug_UpdateCoreState(s_default_claim.thermistor_module,
                              ORION_THERM_SOURCE_ADDR,
                              ORION_BMS_TARGET_ADDR,
                              s_cache.count,
                              s_cache.valid_count,
                              CAN_ModuleFaultActive(&s_cache),
                              s_cache.fault_mask,
                              s_cache.min_temp,
                              s_cache.max_temp,
                              s_cache.avg_temp,
                              s_cache.max_id,
                              s_cache.min_id);
}

/* -------------------------------------------------------------------------- */
/* Encode J1939 Address Claim (0x18EEFF80)                                    */
/* -------------------------------------------------------------------------- */

void EncodeJ1939Claim(uint8_t *payload)
{
    CAN_EncodeJ1939ClaimForModule(ORION_THERM_SOURCE_ADDR,
                                  s_default_claim.thermistor_module,
                                  payload);
}

/* -------------------------------------------------------------------------- */
/* Encode BMS Broadcast (0x1839F380)                                          */
/* Per spec:                                                                  */
/* Byte 0: Thermistor Module Number                                           */
/* Byte 1: Lowest temp (int8_t)                                               */
/* Byte 2: Highest temp (int8_t)                                              */
/* Byte 3: Average temp (int8_t)                                              */
/* Byte 4: Number of thermistors enabled (bit 7 = fault)                      */
/* Byte 5: Highest thermistor ID on module (zero-based)                       */
/* Byte 6: Lowest thermistor ID on module (zero-based)                        */
/* Byte 8: Checksum (sum of all bytes + 0x39 + length)                        */
/* -------------------------------------------------------------------------- */

void EncodeBMSBroadcast(uint8_t *payload)
{
    CAN_EncodeBmsForCache(&s_cache, s_default_claim.thermistor_module, payload);
}

/* -------------------------------------------------------------------------- */
/* Encode General Broadcast (0x1838F380)                                      */
/* Per spec and Orion multi-module support:                                   */
/* Byte 0-1: Global thermistor ID (relative to all configured modules)        */
/* Byte 2: Thermistor value (int8_t, 1C units)                                */
/* Byte 3: Local thermistor ID, bit7 = this thermistor fault                  */
/* Byte 4: Lowest valid thermistor value on module                            */
/* Byte 5: Highest valid thermistor value on module                           */
/* Byte 6: Highest thermistor ID on module (zero-based)                       */
/* Byte 7: Lowest thermistor ID on module (zero-based)                        */
/* -------------------------------------------------------------------------- */

void EncodeGeneralBroadcast(uint8_t therm_index, uint8_t *payload)
{
    CAN_EncodeGeneralForCache(&s_cache, s_default_claim.thermistor_module, therm_index, payload);
}

void CAN_UpdateExternalADCVoltages(const uint16_t *out_mv, uint8_t count)
{
    if (out_mv == NULL) {
        return;
    }

    if (count > MAX_VOLTAGE) {
        count = MAX_VOLTAGE;
    }

    memset(g_can_ctx.voltages.voltage_adc_values, 0, sizeof(g_can_ctx.voltages.voltage_adc_values));
    memcpy(g_can_ctx.voltages.voltage_adc_values, out_mv, (size_t)count * sizeof(uint16_t));
    g_can_ctx.voltages.num_active = count;
}


/* -------------------------------------------------------------------------- */
/* Main Send Function - Call from main loop                                   */
/* -------------------------------------------------------------------------- */

void CAN_SendMessages(void)
{
    static uint8_t therm_index = 0U;
    static uint8_t emu_therm_index[CAN_DEBUG_EMU_MODULES] = {0U, 0U};
    static uint8_t emu_module_slot_rr = 0U;
    static uint8_t emu_claim_slot_rr = 0U;
    static uint8_t ext_voltage_segment_rr = 0U;
    uint8_t payload[CAN_FRAME_LEN_BYTES];
    int result;
    bool sent_claim_this_pass = false;

    /* Ensure we have at least one temperature snapshot before transmitting */
    if (s_cache.count == 0U && g_can_ctx.thermistors.num_active > 0U) {
        ConvertAllThermistors(g_can_ctx.thermistors.thermistor_adc_values,
                              g_can_ctx.thermistors.num_active);
    }

    if (CAN_DebugDualModuleActive()) {
        if (Timer_CheckCan200msFlag()) {
            const uint32_t now_ms = HAL_GetTick();
            const uint8_t module_slot = emu_claim_slot_rr;
            const uint8_t source_addr = (uint8_t)(ORION_THERM_SOURCE_ADDR + module_slot);
            const uint8_t module_index = (uint8_t)(ORION_THERM_MODULE_INDEX + module_slot);
            const uint32_t claim_id = CAN_ClaimIdForSource(source_addr);

            CAN_EncodeJ1939ClaimForModule(source_addr, module_index, payload);
            result = CAN_Comm_SendExt(claim_id, payload, CAN_FRAME_LEN_BYTES);
            CAN_Debug_RecordClaim(payload, now_ms);

            if (result != 0) {
                CAN_LogTxFailure_("claim", claim_id, result);
            } else {
                CAN_Debug_UpdateCoreState(module_index,
                                          source_addr,
                                          ORION_BMS_TARGET_ADDR,
                                          0U,
                                          0U,
                                          false,
                                          0U,
                                          0,
                                          0,
                                          0,
                                          0U,
                                          0U);
                CAN_Debug_RequestLogClaim();
            }
            emu_claim_slot_rr = (uint8_t)((emu_claim_slot_rr + 1U) % CAN_DEBUG_EMU_MODULES);
            sent_claim_this_pass = true;
        }

        if (Timer_CheckCan100msFlag()) {
            const uint32_t now_ms = HAL_GetTick();
            const uint8_t module_slot = emu_module_slot_rr;
            const uint8_t source_addr = (uint8_t)(ORION_THERM_SOURCE_ADDR + module_slot);
            const uint8_t module_index = (uint8_t)(ORION_THERM_MODULE_INDEX + module_slot);
            const uint8_t start_idx = (uint8_t)(module_slot * CAN_DEBUG_EMU_CHANNELS_PER_MODULE);
            const uint8_t module_count = CAN_DebugModuleSampleCount(start_idx);
            const uint32_t bms_id = CAN_BmsIdForSource(source_addr);
            const uint32_t gen_id = CAN_GeneralIdForSource(source_addr);

            ThermistorCache_t module_cache;
            CAN_BuildModuleCacheFromAdc(start_idx, module_count, &module_cache);

            CAN_EncodeBmsForCache(&module_cache, module_index, payload);
            result = CAN_Comm_SendExt(bms_id, payload, CAN_FRAME_LEN_BYTES);
            CAN_Debug_RecordBms(payload, now_ms);
            CAN_Debug_UpdateCoreState(module_index,
                                      source_addr,
                                      ORION_BMS_TARGET_ADDR,
                                      module_cache.count,
                                      module_cache.valid_count,
                                      CAN_ModuleFaultActive(&module_cache),
                                      module_cache.fault_mask,
                                      module_cache.min_temp,
                                      module_cache.max_temp,
                                      module_cache.avg_temp,
                                      module_cache.max_id,
                                      module_cache.min_id);
            if (result != 0) {
                CAN_LogTxFailure_("bms", bms_id, result);
            } else {
                CAN_Debug_RequestLogBms();
            }

            CAN_EncodeGeneralForCache(&module_cache,
                                      module_index,
                                      emu_therm_index[module_slot],
                                      payload);
            result = CAN_Comm_SendExt(gen_id, payload, CAN_FRAME_LEN_BYTES);
            CAN_Debug_RecordGeneral(payload, now_ms);
            CAN_Debug_UpdateCoreState(module_index,
                                      source_addr,
                                      ORION_BMS_TARGET_ADDR,
                                      module_cache.count,
                                      module_cache.valid_count,
                                      CAN_ModuleFaultActive(&module_cache),
                                      module_cache.fault_mask,
                                      module_cache.min_temp,
                                      module_cache.max_temp,
                                      module_cache.avg_temp,
                                      module_cache.max_id,
                                      module_cache.min_id);
            if (result != 0) {
                CAN_LogTxFailure_("gen", gen_id, result);
            } else {
                CAN_Debug_RequestLogGeneral();
            }

            if (module_cache.count > 0U) {
                emu_therm_index[module_slot] =
                    (uint8_t)((emu_therm_index[module_slot] + 1U) % module_cache.count);
            } else {
                emu_therm_index[module_slot] = 0U;
            }

            /* Allow at most one 100 ms deferral when a claim frame shares this slot.
             * The timer event remains pending until we successfully transmit, so timing
             * stays phase-locked instead of drifting with HAL_GetTick()-based gating. */
            if (!sent_claim_this_pass &&
                Timer_HasCanExternalVoltageEvent() &&
                CAN_SendExternalADCVoltageFrame_(ext_voltage_segment_rr, payload)) {
                Timer_ConsumeCanExternalVoltageEvent();
                ext_voltage_segment_rr =
                    (uint8_t)((ext_voltage_segment_rr + 1U) % EXTERNAL_ADC_VOLTAGE_FRAMES);
            }
            emu_module_slot_rr = (uint8_t)((emu_module_slot_rr + 1U) % CAN_DEBUG_EMU_MODULES);
        }

        CAN_Debug_TryLogClaim();
        CAN_Debug_TryLogBms();
        CAN_Debug_TryLogGeneral();
        return;
    }

    /* 200 ms: J1939 Address Claim */
    if (Timer_CheckCan200msFlag()) {
        EncodeJ1939Claim(payload);
        result = CAN_Comm_SendExt(THERM_J1939_CLAIM_ID, payload, CAN_FRAME_LEN_BYTES);
        CAN_Debug_RecordClaim(payload, HAL_GetTick());
        if (result != 0) {
            CAN_LogTxFailure_("claim", THERM_J1939_CLAIM_ID, result);
        } else {
            CAN_Debug_RequestLogClaim();
        }
        sent_claim_this_pass = true;
    }

    /* 100 ms: BMS Broadcast + General Broadcast */
    if (Timer_CheckCan100msFlag()) {
        const uint32_t now_ms = HAL_GetTick();
        /* Send BMS Broadcast */
        EncodeBMSBroadcast(payload);
        result = CAN_Comm_SendExt(THERM_BMS_BROADCAST_ID, payload, CAN_FRAME_LEN_BYTES);

        CAN_Debug_RecordBms(payload, now_ms);
        CAN_Debug_UpdateCoreState(s_default_claim.thermistor_module,
                      ORION_THERM_SOURCE_ADDR,
                      ORION_BMS_TARGET_ADDR,
                      s_cache.count,
                      s_cache.valid_count,
                      CAN_ModuleFaultActive(&s_cache),
                      s_cache.fault_mask,
                      s_cache.min_temp,
                      s_cache.max_temp,
                      s_cache.avg_temp,
                      s_cache.max_id,
                      s_cache.min_id);

        if (result != 0) {
            CAN_LogTxFailure_("bms", THERM_BMS_BROADCAST_ID, result);
        } else {
            CAN_Debug_RequestLogBms();
        }

        /* Send General Broadcast (round-robin) */
        EncodeGeneralBroadcast(therm_index, payload);
        result = CAN_Comm_SendExt(THERM_GENERAL_BROADCAST_ID, payload, CAN_FRAME_LEN_BYTES);

        CAN_Debug_RecordGeneral(payload, now_ms);
        CAN_Debug_UpdateCoreState(s_default_claim.thermistor_module,
                      ORION_THERM_SOURCE_ADDR,
                      ORION_BMS_TARGET_ADDR,
                      s_cache.count,
                      s_cache.valid_count,
                      CAN_ModuleFaultActive(&s_cache),
                      s_cache.fault_mask,
                      s_cache.min_temp,
                      s_cache.max_temp,
                      s_cache.avg_temp,
                      s_cache.max_id,
                      s_cache.min_id);

        if (result != 0) {
            CAN_LogTxFailure_("gen", THERM_GENERAL_BROADCAST_ID, result);
        } else {
            CAN_Debug_RequestLogGeneral();
        }

        if (!sent_claim_this_pass &&
            Timer_HasCanExternalVoltageEvent() &&
            CAN_SendExternalADCVoltageFrame_(ext_voltage_segment_rr, payload)) {
            Timer_ConsumeCanExternalVoltageEvent();
            ext_voltage_segment_rr =
                (uint8_t)((ext_voltage_segment_rr + 1U) % EXTERNAL_ADC_VOLTAGE_FRAMES);
        }

        /* Next thermistor */
        if (s_cache.count > 0U) {
            therm_index = (uint8_t)((therm_index + 1U) % s_cache.count);
        }
    }

    /* Emit any pending debug logs (set via interrupt or success paths) */
    CAN_Debug_TryLogClaim();
    CAN_Debug_TryLogBms();
    CAN_Debug_TryLogGeneral();
}
