KaylaR2040/SD_OrionBMS/src/can.c

/*
 * ===========================================================================
 * File: can.c
 * Description: High-level CAN messaging helpers following CMU guidelines.
 * ===========================================================================
 */

#include "master.h"
#include <stdio.h>
#include <string.h>

// Init Variables
FDCAN_HandleTypeDef g_fdcan1;
FDCAN_TxHeaderTypeDef g_can_tx_header;
uint8_t g_can_tx_data[CAN_MAX_DLEN_BYTES];
can_app_ctx_t g_can_ctx;
static bool s_can_scheduling_enabled = false;

// OLD Time Query based Implmentation
// static bool CAN_ShouldLogTxError_(void)
// {
//     static uint32_t last_tx_error_log_ms = 0U;
//     const uint32_t now = HAL_GetTick();

//     if ((now - last_tx_error_log_ms) >= CAN_TX_ERROR_LOG_PERIOD_MS) {
//         last_tx_error_log_ms = now;
//         return true;
//     }
//     return false;
// }

// New Interrupt based Implementation
// TODO KAYLA: Please review. Are we sure that we should only be checking for TX errors when log is sent out, not with every CAN message?
static bool CAN_ShouldLogTxError_(void){
    /* CAN TX errors are logged when Timer_CheckLogOffset2Flag() fires (every 3s, at the 3s mark) */
    return Timer_CheckLogOffset2Flag();
}


/* -------------------------------------------------------------------------- */
/* BITRATE FDCAN CONFIGURATION                          */
/* -------------------------------------------------------------------------- */
void CAN_App_Init(uint32_t kbps)
{
    uint32_t init_kbps = kbps;
    if (init_kbps == 0U) {
        init_kbps = CAN_APP_DEFAULT_KBPS;
    }

    if (CAN_Comm_Init_kbps(init_kbps) != 0) {
        LOG_PRINT(LOG_TYPE_ERROR, "FDCAN init failed");
        Error_Handler();
    }

    s_can_scheduling_enabled = false;
}


int CAN_Comm_Init_kbps(uint32_t kbps)
{
    uint32_t bitrate_hz = kbps * 1000U;
    uint32_t presc = 0U, tseg1 = 0U, tseg2 = 0U, sjw = 0U;

    if (CAN_FindTiming(CAN_FDCAN_KERNEL_CLK_HZ, bitrate_hz, &presc, &tseg1, &tseg2, &sjw) != 0) {
        const uint32_t tq = CAN_TIMING_FALLBACK_TQ;
        uint32_t presc_try = (CAN_FDCAN_KERNEL_CLK_HZ + (bitrate_hz * tq) / 2U) / (bitrate_hz * tq);
        if (presc_try < CAN_TIMING_PRESC_MIN) {
            presc_try = CAN_TIMING_PRESC_MIN;
        }
        if (presc_try > CAN_TIMING_PRESC_MAX) {
            presc_try = CAN_TIMING_PRESC_MAX;
        }
        presc = presc_try;
        uint32_t tseg_total = tq - 1U;
        uint32_t tseg2_candidate = tseg_total / CAN_TIMING_TSEG2_DIVISOR;
        if (tseg2_candidate != 0U) {
            tseg2 = tseg2_candidate;
        } else {
            tseg2 = CAN_TIMING_TSEG2_MIN;
        }
        tseg1 = tseg_total - tseg2;
        if (tseg2 >= CAN_TIMING_SJW_MAX) {
            sjw = CAN_TIMING_SJW_MAX;
        } else {
            sjw = tseg2;
        }
    }

    LOG_PRINT(LOG_TYPE_INFO, "FDCAN nominal timing: %lu kbps presc=%lu tseg1=%lu tseg2=%lu sjw=%lu",
             (unsigned long)kbps,
             (unsigned long)presc,
             (unsigned long)tseg1,
             (unsigned long)tseg2,
             (unsigned long)sjw);

    g_fdcan1.Instance = FDCAN1;
    g_fdcan1.Init.FrameFormat = FDCAN_FRAME_CLASSIC;
    g_fdcan1.Init.Mode = FDCAN_MODE_NORMAL;
    g_fdcan1.Init.AutoRetransmission = ENABLE;
    g_fdcan1.Init.TransmitPause = DISABLE;
    g_fdcan1.Init.ProtocolException = DISABLE;

    g_fdcan1.Init.NominalPrescaler = presc;
    g_fdcan1.Init.NominalSyncJumpWidth = sjw;
    g_fdcan1.Init.NominalTimeSeg1 = tseg1;
    g_fdcan1.Init.NominalTimeSeg2 = tseg2;

    g_fdcan1.Init.DataPrescaler = CAN_FD_DATA_TIMING_DEFAULT;
    g_fdcan1.Init.DataSyncJumpWidth = CAN_FD_DATA_TIMING_DEFAULT;
    g_fdcan1.Init.DataTimeSeg1 = CAN_FD_DATA_TIMING_DEFAULT;
    g_fdcan1.Init.DataTimeSeg2 = CAN_FD_DATA_TIMING_DEFAULT;

    if (HAL_FDCAN_Init(&g_fdcan1) != HAL_OK) {
        return -1;
    }

    FDCAN_FilterTypeDef sFilterConfig;
    sFilterConfig.IdType = FDCAN_STANDARD_ID;
    sFilterConfig.FilterIndex = CAN_FILTER_INDEX_DEFAULT;
    sFilterConfig.FilterType = FDCAN_FILTER_RANGE;
    sFilterConfig.FilterConfig = FDCAN_FILTER_TO_RXFIFO0;
    sFilterConfig.FilterID1 = CAN_STD_FILTER_ID_MIN;
    sFilterConfig.FilterID2 = CAN_STD_FILTER_ID_MAX;
    if (HAL_FDCAN_ConfigFilter(&g_fdcan1, &sFilterConfig) != HAL_OK) {
        return -1;
    }

    FDCAN_FilterTypeDef xFilterConfig;
    xFilterConfig.IdType = FDCAN_EXTENDED_ID;
    xFilterConfig.FilterIndex = CAN_FILTER_INDEX_DEFAULT;
    xFilterConfig.FilterType = FDCAN_FILTER_RANGE;
    xFilterConfig.FilterConfig = FDCAN_FILTER_TO_RXFIFO0;
    xFilterConfig.FilterID1 = CAN_EXT_FILTER_ID_MIN;
    xFilterConfig.FilterID2 = CAN_EXT_FILTER_ID_MAX;
    if (HAL_FDCAN_ConfigFilter(&g_fdcan1, &xFilterConfig) != HAL_OK) {
        return -1;
    }

    if (HAL_FDCAN_Start(&g_fdcan1) != HAL_OK) {
        return -1;
    }

    CAN_App_InitData(&g_can_ctx);
    return 0;
}

// Initalize the CAN content
void CAN_App_InitData(can_app_ctx_t *ctx)
{
    if (!ctx) return;

    memset(ctx, 0, sizeof(*ctx));

    ctx->thermistors.num_active = 0;

    /* Prevent immediate sends on startup by stamping timestamps to now */
    uint32_t now = HAL_GetTick();
    ctx->last_claim_ms = now;
    ctx->last_bms_ms = now;
    ctx->last_general_ms = now;

    ctx->therm_index = 0; 

    uint32_t err = HAL_FDCAN_GetError(&g_fdcan1);
    LOG_PRINT(LOG_TYPE_INFO, "ERROR CODE AFTER INIT: 0x%08lX", (unsigned long)err);
}

void CAN_SetSchedulingEnabled(bool enabled, bool send_immediately)
{
    s_can_scheduling_enabled = enabled;
    Timer_ResetCanSchedule();

    if (enabled && send_immediately) {
        Timer_TriggerCanScheduleNow();
    }
}

bool CAN_IsSchedulingEnabled(void)
{
    return s_can_scheduling_enabled;
}

//TODO: This should be changed to use an interrupt instead of the next sample and now thing.. 
void CAN_ServiceTask(void)
{
    /* Check if CAN subsystem is active */
    if (can_status == FAILED || !s_can_scheduling_enabled) {
        LED_On(CAN_LED);  /* Light up CAN_LED on CAN failure */
        // return; // Commented out to ensure CAN Service routine ALWAYS runs, even if CAN is in a failed state
    }

    CAN_SendMessages();
    
}



/* -------------------------------------------------------------------------- */
/* CAN Communication Helper Functions                           */
/* -------------------------------------------------------------------------- */

/** Attempt to derive timing parameters for the requested bitrate. */
int CAN_FindTiming(uint32_t fclk_hz, uint32_t bitrate_hz,
                          uint32_t *out_presc, uint32_t *out_tseg1,
                          uint32_t *out_tseg2, uint32_t *out_sjw)
{
    for (uint32_t tq = CAN_TIMING_TQ_MIN; tq <= CAN_TIMING_TQ_MAX; ++tq) {
        for (uint32_t presc = CAN_TIMING_PRESC_MIN; presc <= CAN_TIMING_PRESC_MAX; ++presc) {
            uint64_t num = (uint64_t)fclk_hz;
            uint64_t den = (uint64_t)presc * (uint64_t)tq;
            if (den == 0U) {
                continue;
            }
            if (num % den != 0U) {
                continue;
            }
            uint32_t calc = (uint32_t)(num / den);
            if (calc != bitrate_hz) {
                continue;
            }
            uint32_t tseg_total = tq - 1U;
            uint32_t tseg2 = tseg_total / CAN_TIMING_TSEG2_DIVISOR;
            if (tseg2 < CAN_TIMING_TSEG2_MIN) {
                tseg2 = CAN_TIMING_TSEG2_MIN;
            }
            uint32_t tseg1 = tseg_total - tseg2;
            if (tseg1 < CAN_TIMING_TSEG1_MIN || tseg1 > CAN_TIMING_TSEG1_MAX) {
                continue;
            }
            uint32_t sjw;
            if (tseg2 >= CAN_TIMING_SJW_MAX) {
                sjw = CAN_TIMING_SJW_MAX;
            } else {
                sjw = tseg2;
            }
            *out_presc = presc;
            *out_tseg1 = tseg1;
            *out_tseg2 = tseg2;
            *out_sjw = sjw;
            return 0;
        }
    }
    return -1;
}



/* Send an extended (29-bit) CAN frame for J1939/BMS messages */
int CAN_Comm_SendExt(uint32_t ext_id, const uint8_t *data, uint8_t len)
{
    if (len > CAN_MAX_DLEN_BYTES) {
        return -1;
    }

    FDCAN_TxHeaderTypeDef txHeader;
    txHeader.Identifier = ext_id & CAN_EXT_ID_MASK;
    txHeader.IdType = FDCAN_EXTENDED_ID;
    txHeader.TxFrameType = FDCAN_DATA_FRAME;

    switch (len) {
        case 0: txHeader.DataLength = FDCAN_DLC_BYTES_0; break;
        case 1: txHeader.DataLength = FDCAN_DLC_BYTES_1; break;
        case 2: txHeader.DataLength = FDCAN_DLC_BYTES_2; break;
        case 3: txHeader.DataLength = FDCAN_DLC_BYTES_3; break;
        case 4: txHeader.DataLength = FDCAN_DLC_BYTES_4; break;
        case 5: txHeader.DataLength = FDCAN_DLC_BYTES_5; break;
        case 6: txHeader.DataLength = FDCAN_DLC_BYTES_6; break;
        case 7: txHeader.DataLength = FDCAN_DLC_BYTES_7; break;
        default: txHeader.DataLength = FDCAN_DLC_BYTES_8; break;
    }

#if defined(FDCAN_ERROR_STATE_ACTIVE)
    txHeader.ErrorStateIndicator = FDCAN_ERROR_STATE_ACTIVE;
#elif defined(FDCAN_ERROR_STATE_NORMAL)
    txHeader.ErrorStateIndicator = FDCAN_ERROR_STATE_NORMAL;
#else
    txHeader.ErrorStateIndicator = CAN_TX_MESSAGE_MARKER_DEFAULT;
#endif

    txHeader.BitRateSwitch = FDCAN_BRS_OFF;
    txHeader.FDFormat = FDCAN_CLASSIC_CAN;
    txHeader.TxEventFifoControl = FDCAN_NO_TX_EVENTS;
    txHeader.MessageMarker = CAN_TX_MESSAGE_MARKER_DEFAULT;


    if (HAL_FDCAN_AddMessageToTxFifoQ(&g_fdcan1, &txHeader, (uint8_t *)data) != HAL_OK) {
        if (CAN_ShouldLogTxError_()) {
            if ((g_fdcan1.ErrorCode & HAL_FDCAN_ERROR_FIFO_FULL) != 0u) {
                LOG_PRINT(LOG_TYPE_WARN, "FDCAN TX FIFO full ID=0x%08lX free=%lu state=%lu",
                         (unsigned long)ext_id,
                         (unsigned long)HAL_FDCAN_GetTxFifoFreeLevel(&g_fdcan1),
                         (unsigned long)HAL_FDCAN_GetState(&g_fdcan1));
            } else {
                LOG_PRINT(LOG_TYPE_WARN, "FDCAN TX add failed ID=0x%08lX err=0x%08lX state=%lu",
                         (unsigned long)ext_id,
                         (unsigned long)g_fdcan1.ErrorCode,
                         (unsigned long)HAL_FDCAN_GetState(&g_fdcan1));
            }
        }
        return CAN_TX_RESULT_TRANSIENT_DROP;
    }
    return 0;
}
