KaylaR2040/SD_OrionBMS/TI_Ref_Code/bq79616_sample_code/source/notification.c

/** @file notification.c 
*   @brief User Notification Definition File
*   @date 07-July-2017
*   @version 04.07.00
*
*   This file  defines  empty  notification  routines to avoid
*   linker errors, Driver expects user to define the notification. 
*   The user needs to either remove this file and use their custom 
*   notification function or place their code sequence in this file 
*   between the provided USER CODE BEGIN and USER CODE END.
*
*/

/* 
* Copyright (C) 2009-2016 Texas Instruments Incorporated - www.ti.com 
* 
* 
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
*    Redistributions of source code must retain the above copyright 
*    notice, this list of conditions and the following disclaimer.
*
*    Redistributions in binary form must reproduce the above copyright
*    notice, this list of conditions and the following disclaimer in the 
*    documentation and/or other materials provided with the   
*    distribution.
*
*    Neither the name of Texas Instruments Incorporated nor the names of
*    its contributors may be used to endorse or promote products derived
*    from this software without specific prior written permission.
*
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
*/


/* Include Files */

#include "esm.h"
#include "sys_selftest.h"
#include "gio.h"
#include "sci.h"
#include "rti.h"
#include "sys_dma.h"

/* USER CODE BEGIN (0) */
extern int UART_RX_RDY;
extern int RTI_TIMEOUT;
/* USER CODE END */
#pragma WEAK(esmGroup1Notification)
void esmGroup1Notification(uint32 channel)
{
/*  enter user code between the USER CODE BEGIN and USER CODE END. */
/* USER CODE BEGIN (1) */
/* USER CODE END */
}

/* USER CODE BEGIN (2) */
/* USER CODE END */
#pragma WEAK(esmGroup2Notification)
void esmGroup2Notification(uint32 channel)
{
/*  enter user code between the USER CODE BEGIN and USER CODE END. */
/* USER CODE BEGIN (3) */
/* USER CODE END */
}

/* USER CODE BEGIN (4) */
/* USER CODE END */
#pragma WEAK(memoryPort0TestFailNotification)
void memoryPort0TestFailNotification(uint32 groupSelect, uint32 dataSelect, uint32 address, uint32 data)
{
/*  enter user code between the USER CODE BEGIN and USER CODE END. */
/* USER CODE BEGIN (5) */
/* USER CODE END */
}

/* USER CODE BEGIN (6) */
/* USER CODE END */
#pragma WEAK(memoryPort1TestFailNotification)
void memoryPort1TestFailNotification(uint32 groupSelect, uint32 dataSelect, uint32 address, uint32 data)
{
/*  enter user code between the USER CODE BEGIN and USER CODE END. */
/* USER CODE BEGIN (7) */
/* USER CODE END */
}

/* USER CODE BEGIN (8) */
/* USER CODE END */
#pragma WEAK(rtiNotification)
void rtiNotification(uint32 notification)
{
/*  enter user code between the USER CODE BEGIN and USER CODE END. */
/* USER CODE BEGIN (9) */
    RTI_TIMEOUT = 1;
/* USER CODE END */
}

/* USER CODE BEGIN (10) */
/* USER CODE END */
#pragma WEAK(gioNotification)
void gioNotification(gioPORT_t *port, uint32 bit)
{
/*  enter user code between the USER CODE BEGIN and USER CODE END. */
/* USER CODE BEGIN (19) */
/* USER CODE END */
}

/* USER CODE BEGIN (20) */
/* USER CODE END */

#pragma WEAK(sciNotification)
void sciNotification(sciBASE_t *sci, uint32 flags)     
{
/*  enter user code between the USER CODE BEGIN and USER CODE END. */
/* USER CODE BEGIN (29) */
    UART_RX_RDY = 1;
    sciREG->CLEARINT = SCI_RX_INT;
/* USER CODE END */
}

/* USER CODE BEGIN (30) */
/* USER CODE END */



/* USER CODE BEGIN (43) */
/* USER CODE END */


/* USER CODE BEGIN (47) */
/* USER CODE END */


/* USER CODE BEGIN (50) */
/* USER CODE END */


/* USER CODE BEGIN (53) */
/* USER CODE END */

#pragma WEAK(dmaGroupANotification)
void dmaGroupANotification(dmaInterrupt_t inttype, uint32 channel)
{
/*  enter user code between the USER CODE BEGIN and USER CODE END. */
/* USER CODE BEGIN (54) */
/* USER CODE END */
}
/* USER CODE BEGIN (55) */
/* USER CODE END */

/* USER CODE BEGIN (56) */
/* USER CODE END */

/* USER CODE BEGIN (58) */
/* USER CODE END */

/* USER CODE BEGIN (60) */
/* USER CODE END */
