KaylaR2040/SD_OrionBMS/TI_Ref_Code/bq79616_sample_code/include/bq79616.h

/*
 *  @file bq79616.h
 *
 *  @author Vince Toledo - Texas Instruments Inc.
 *  @date February 2020
 *  @version 1.2
 *  @note Built with CCS for Hercules Version: 8.1.0.00011
 *  @note Built for TMS570LS1224 (LAUNCH XL2)
 */

/*****************************************************************************
**
**  Copyright (c) 2011-2019 Texas Instruments
**
******************************************************************************/


#ifndef BQ79616_H_
#define BQ79616_H_

#include "datatypes.h"
#include "hal_stdtypes.h"

//****************************************************
// ***Register defines, choose one of the following***
// ***based on your device silicon revision:       ***
//****************************************************
//#include "A0_reg.h"
#include "B0_reg.h"

// User defines
#define TOTALBOARDS 1       //boards in stack
#define MAXBYTES (16*2)     //maximum number of bytes to be read from the devices (for array creation)
#define BAUDRATE 1000000    //device + uC baudrate

#define FRMWRT_SGL_R	0x00    //single device READ
#define FRMWRT_SGL_W	0x10    //single device WRITE
#define FRMWRT_STK_R	0x20    //stack READ
#define FRMWRT_STK_W	0x30    //stack WRITE
#define FRMWRT_ALL_R	0x40    //broadcast READ
#define FRMWRT_ALL_W	0x50    //broadcast WRITE
#define FRMWRT_REV_ALL_W 0x60   //broadcast WRITE reverse direction
                  
// Function Prototypes
void Wake79616();
void AutoAddress();
BOOL GetFaultStat();

uint16 CRC16(BYTE *pBuf, int nLen);

int  WriteReg(BYTE bID, uint16 wAddr, uint64 dwData, BYTE bLen, BYTE bWriteType);
int  ReadReg(BYTE bID, uint16 wAddr, BYTE * pData, BYTE bLen, uint32 dwTimeOut, BYTE bWriteType);

int  WriteFrame(BYTE bID, uint16 wAddr, BYTE * pData, BYTE bLen, BYTE bWriteType);
int  ReadFrameReq(BYTE bID, uint16 wAddr, BYTE bByteToReturn,BYTE bWriteType);
int  WaitRespFrame(BYTE *pFrame, uint32 bLen, uint32 dwTimeOut);

void delayms(uint16 ms);
void delayus(uint16 us);

void ResetAllFaults(BYTE bID, BYTE bWriteType);
void MaskAllFaults(BYTE bID, BYTE bWriteType);

void RunCB();
void ReverseAddressing();

#endif /* BQ79606_H_ */
//EOF
